eddyem/stm32samples/F1:F103/Hall_linear/readme

Take data from "Novotechnik TFD-4000" hall transducer and send it over CAN bus.
