eddyem/stm32samples/F0:F030,F042,F072/usbcan_ringbuffer/Readme.md

Simple code for CAN/USB development board
Simultaneous work of USB CDC (PL2303 emulation) and CAN

Pinout:
PB0 - LED0 - short blink when message received 
PB1 - LED1 - shine when line OK

PB8, PB9 - CAN Rx/Tx

PA11, PA12 - USB DM/DP
