eddyem/stm32samples/G0:G070,G0B1/RTC/README

Simplest work with RTC

Proto:

C - set/print calibration ticks (-511..+512) to each 2^20 ticks
Sd - set date (YY MM DD Weekday)
St - set time (HH MM SS)
t - print current Tms
T - print current Time

Button press - print current time @ usart3
