eddyem/stm32samples/F4:F401/blink/Readme

Simple blink with LED on PC13 (Olimex E407 development board)
