eddyem/stm32samples/F1:F103/canUART/Readme.md

CAN bus (PB8/PB9) <> UART1 (PA9/PA10)
The same thing as canusb for STM32F0x2

Baudrate - 921600
