eddyem/stm32samples/F3:F303/usart1fullDMA/Readme

Full Rx and Tx DMA, Rx DMA ends on buffer end or when '\n' received by character match interrupt.
