eddyem/stm32samples/F1:F103/RGB_LED_Screen/Readme

HUB75E-based RGB LED panel management

886 color (RRRGGGBB)

// the better fonts management is in Chronometer-v3
