eddyem/stm32samples/F1:F103/DS18/Readme

Timer1 + DMA to work with DS18/DHT11 sensors
#define DHT11 in dht.h to change data format to DHT11
