eddyem/stm32samples/F1:F103/BMP180/Readme

Work with I2C temperature/pressure sensor BMP180
