eddyem/stm32samples/F1:F103/BMP280/Readme

Work with I2C temperature/pressure sensor BMP280 and temp/pres/humidity sensor BME280
