eddyem/stm32samples/F1:F103/DHT22_DHT11/Readme

Timer1 + DMA to work with DHT22/DHT11 sensors
#define DHT11 in dht.h to change data format to DHT11
