eddyem/stm32samples/F1:F103/SI7005_HTU21D/Readme

Work with I2C humidity/temperature sensors SI7005 & HTU21D
