eddyem/stm32samples/F1:F103/pl2303_snippet/Readme

Base USB-CDC snippet with PL2303 emulation
With functions of integer read & decimal print.
