eddyem/stm32samples/F1:F103/pwmtest/Readme

Generate signals on PA8 by PWM @ TIM1_CC1.
