eddyem/stm32samples/F0:F030,F042,F072/Snippets/Readme.md

Some snippets
=============

* Flash_EEPROM - EEPROM emulation in flash
* Jump2Boot.c - software init of bootloader
* printuhex.c - print uint32_t in HEX
* readint.c - read integer number in any (bin/hex/dec) system
