eddyem/stm32samples/F1:F103/LED_Screen/Readme

Management with matrixes of LED screens 32x16 (or another size) pixels (P10).
