eddyem/stm32samples/F0:F030,F042,F072/pl2303/Readme.md

Simple CDC for USB development board, emulates PL2303
