eddyem/stm32samples/F1:F103/uart/README

Toggle LED PB9 on STM32F103 development board once per second
Allow to turn on/off LED PB8 depending on user commands over USART (0/1) and check its state (s)
Show information in USART console about S2/S3 buttons pressed
USART: 115200 8n1
