eddyem/stm32samples/F0:F030,F042,F072/tsys01_nucleo/Readme

Example for STM32F042 nucleo working with TSYS-01 temperature sensor.
Every 5 second check temperature on two sensors with different addresses and show values by USART.
USART speed 115200.
