eddyem/stm32samples/F0:F030,F042,F072/htu21d_nucleo/Readme

Example for STM32F042 nucleo working with HTU-21D humidity/temperature sensor.
Every 1 second check humidity/temperature and show values by USART.
USART speed 115200.
