eddyem/stm32samples/F0:F030,F042,F072/blink/README

Toggle Green LED on STM32F042-nucleo depending on jumper @ D2 (PA12):
- no jumper == 'SOS' in Morze
- with jumper - blink with period of 4 seconds
