eddyem/stm32samples/F0/uart/Readme

This is a simple USART over DMA application with hardware end of string control.
Speed 115200. Received string echoes back in reverce order.
