eddyem/stm32samples/F1/GPIO_TIM/README

simple FSMC emulation by timer interrupts
