eddyem/stm32samples/F1/2.8TFT/README

Template of USB-CDC

written for chinese devboard based on STM32F103R8T6

Press H for help
