eddyem/stm32samples/F1/keyboard_snippet/Readme.md

### USB HID keyboard snippet

This snippet allows to emulate USB keyboard to send different messages as they where typed on simple keyboard
(usefull for multiplatform usage without any drivers setup)
