eddyem/stm32samples/F1/GPS+ultrasonic/README

GPS-based timelapse tool
Connect up to four sensors (ultrasonic, infrared, laser and simple switch)
and get precision (milliseconds) time of their signals

written for chinese devboard based on STM32F103RBT6

Press H for help
