eddyem/stm32samples/F1/GPS/README

NOT READY!

GPS RTC

written for chinese devboard based on STM32F103RBT6

Press H for help
