eddyem/stm32samples/F1/simple_cdc/README

Very simple USB-CDC

written for chinese devboard based on STM32F103RBT6

Press H for help
