eddyem/stm32samples/F0:F030,F042,F072/CANbus_stepper/kicad/Readme.md

# CAN bus stepper controller

Move one stepper (12..36V) by CAN or USB bus.
