eddyem/stm32samples/F0:F030,F042,F072/3steppersLB/stepper_driver/04.jpg

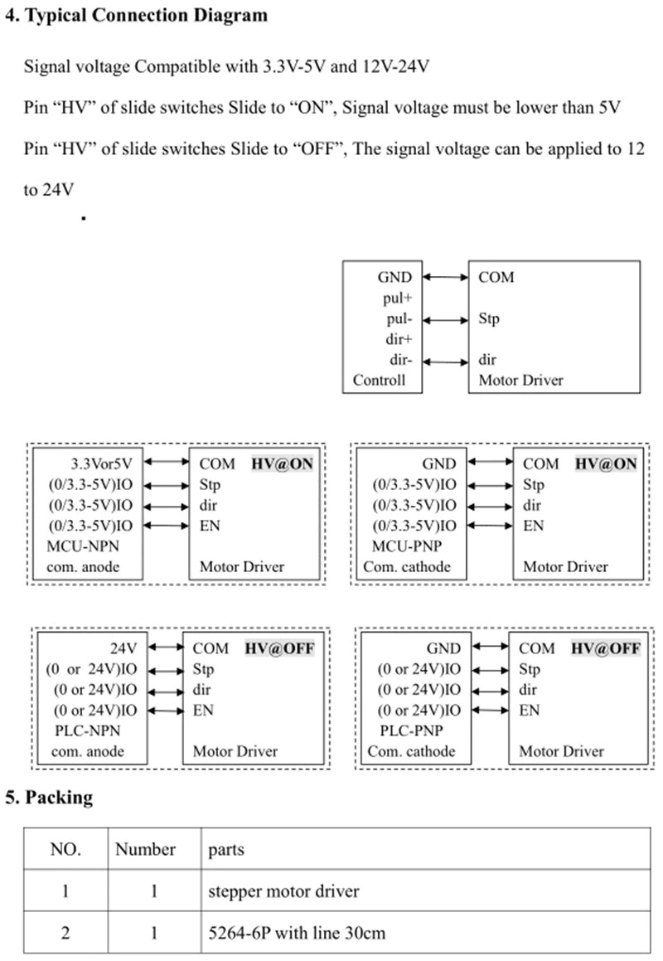
F0:F030,F042,F072/3steppersLB/stepper_driver/04.jpg
