eddyem/stm32samples/F0:F030,F042,F072/Chiller/kicad/Chiller_controlb.png

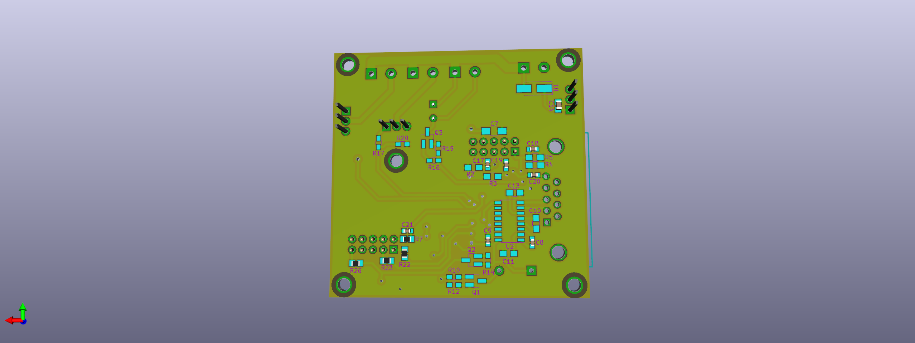
F0:F030,F042,F072/Chiller/kicad/Chiller_controlb.png
