eddyem/stm32samples/F0:F030,F042,F072/Socket_fans/knots/piecevise_files/6NNZZQ4uBDQ.jpg

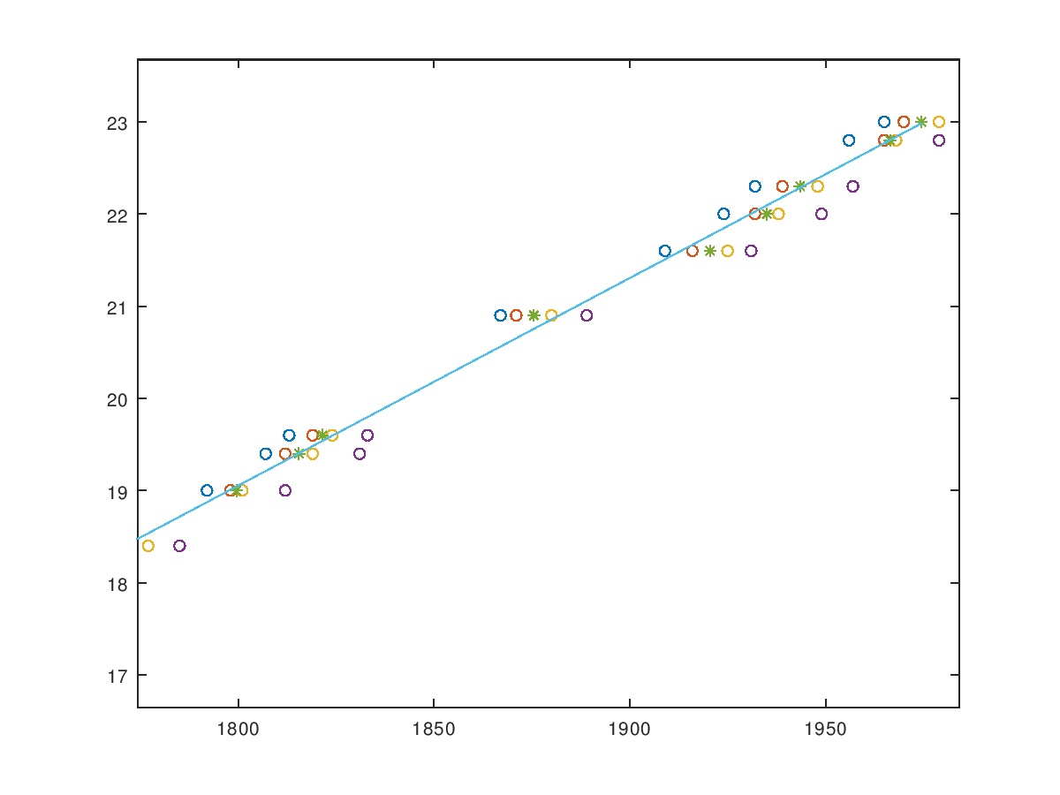
F0:F030,F042,F072/Socket_fans/knots/piecevise_files/6NNZZQ4uBDQ.jpg
