eddyem/stm32samples/F0:F030,F042,F072/Socket_fans/knots/piecevise_files/aLpoeyGgLuE.jpg

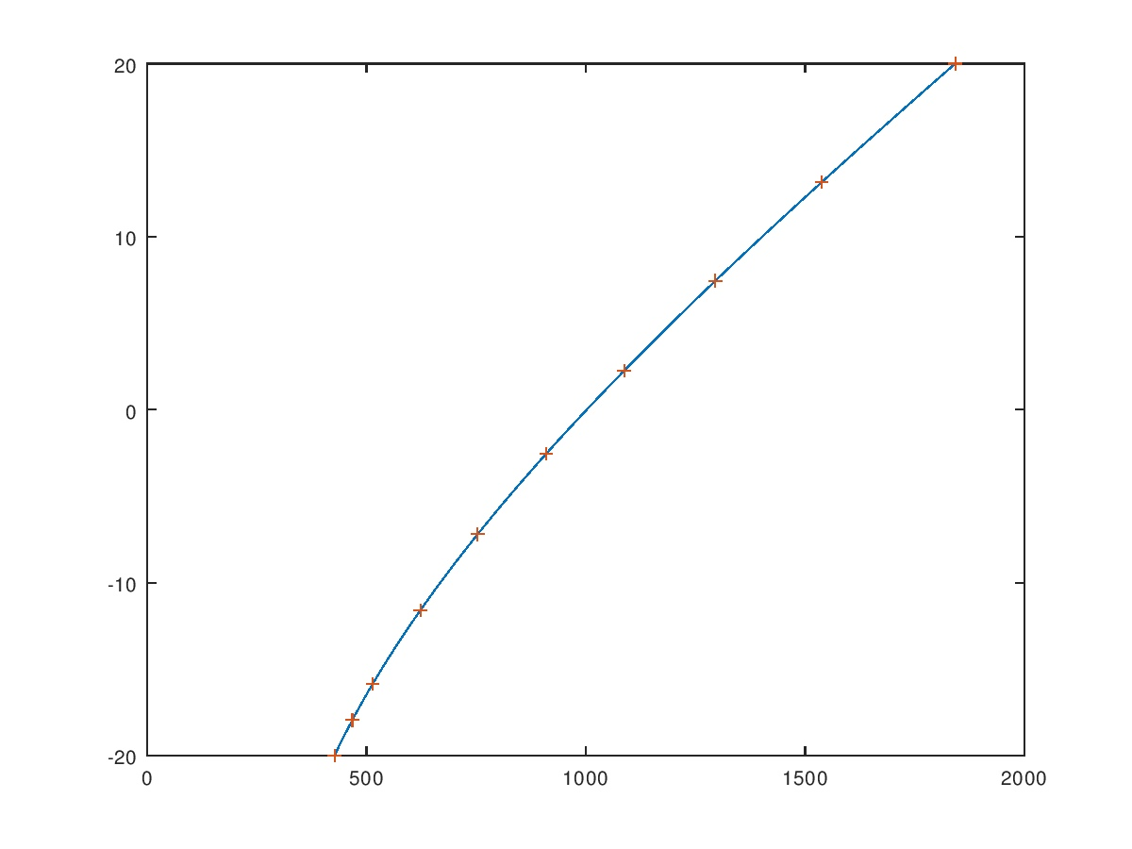
F0:F030,F042,F072/Socket_fans/knots/piecevise_files/aLpoeyGgLuE.jpg
