eddyem/stm32samples/F0:F030,F042,F072/Socket_fans/knots/piecevise_files/Dt9WEEJl_K8.jpg

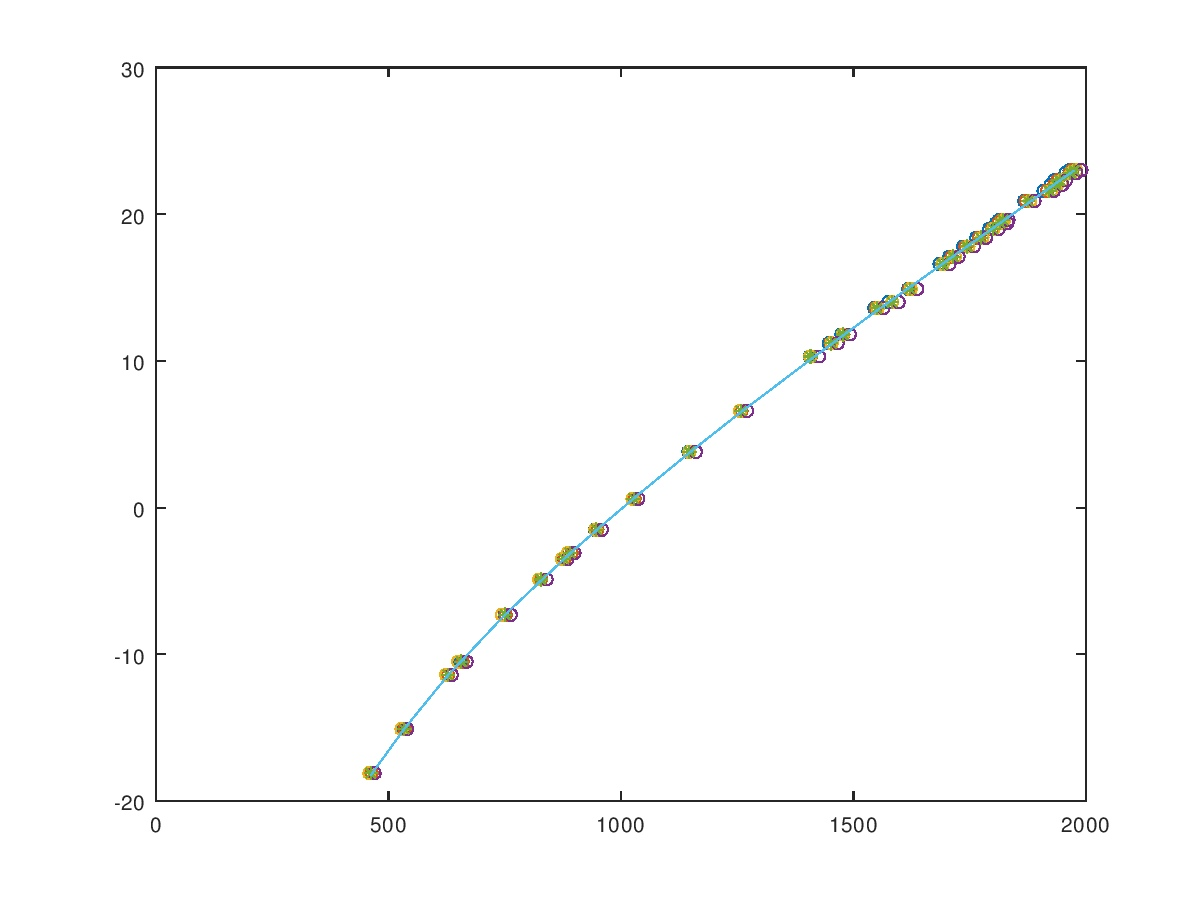
F0:F030,F042,F072/Socket_fans/knots/piecevise_files/Dt9WEEJl_K8.jpg
