eddyem/stm32samples/F0:F030,F042,F072/usbcan/kicad_new/Back.jpg

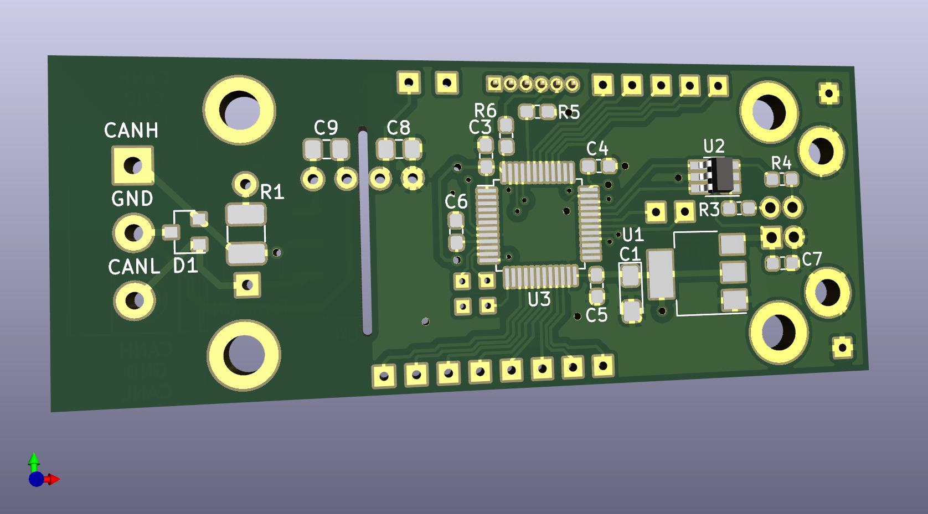
F0:F030,F042,F072/usbcan/kicad_new/Back.jpg
