eddyem/stm32samples/F0:F030,F042,F072/usbcan/kicad_new/Front.jpg

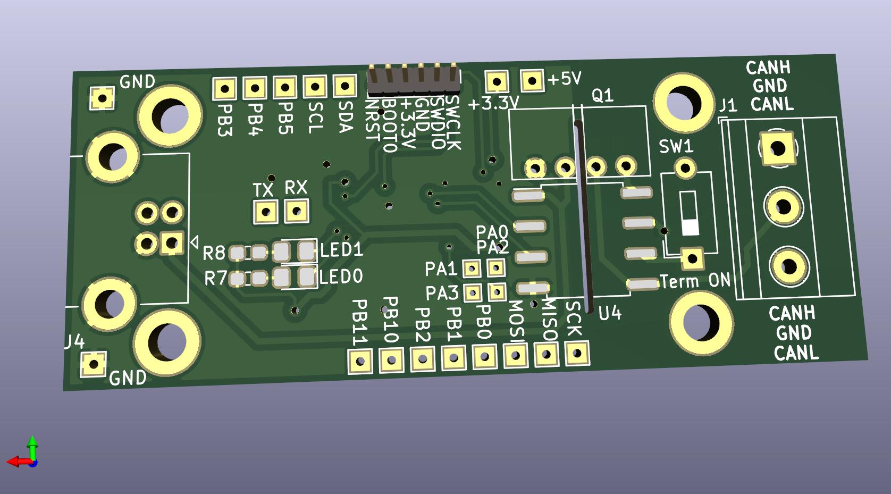
F0:F030,F042,F072/usbcan/kicad_new/Front.jpg
