eddyem/stm32samples/F0:F030,F042,F072/usbcan_relay/kicad/Board3D-back.jpg

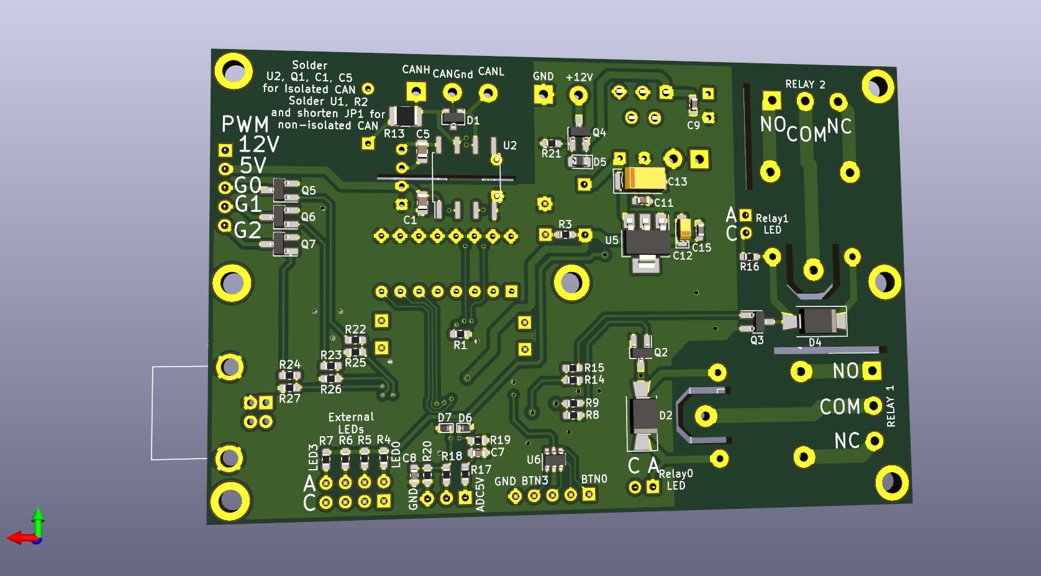
F0:F030,F042,F072/usbcan_relay/kicad/Board3D-back.jpg
