eddyem/stm32samples/F1:F103/CAR_CANbus/WindShield/kicad/Front.jpg

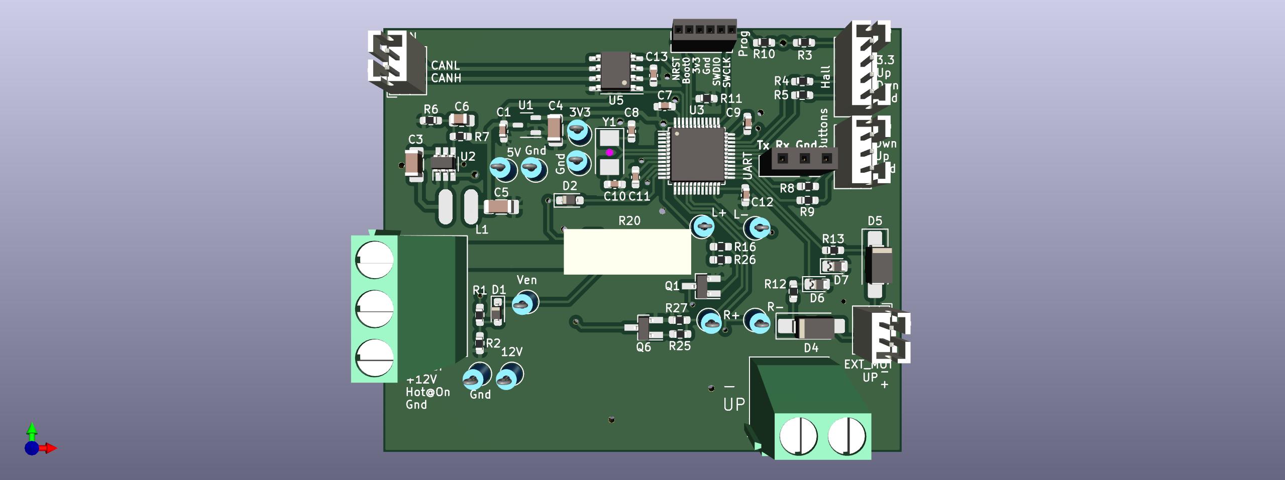
F1:F103/CAR_CANbus/WindShield/kicad/Front.jpg
