eddyem/stm32samples/F1:F103/RGB_LED_Screen/histo.png

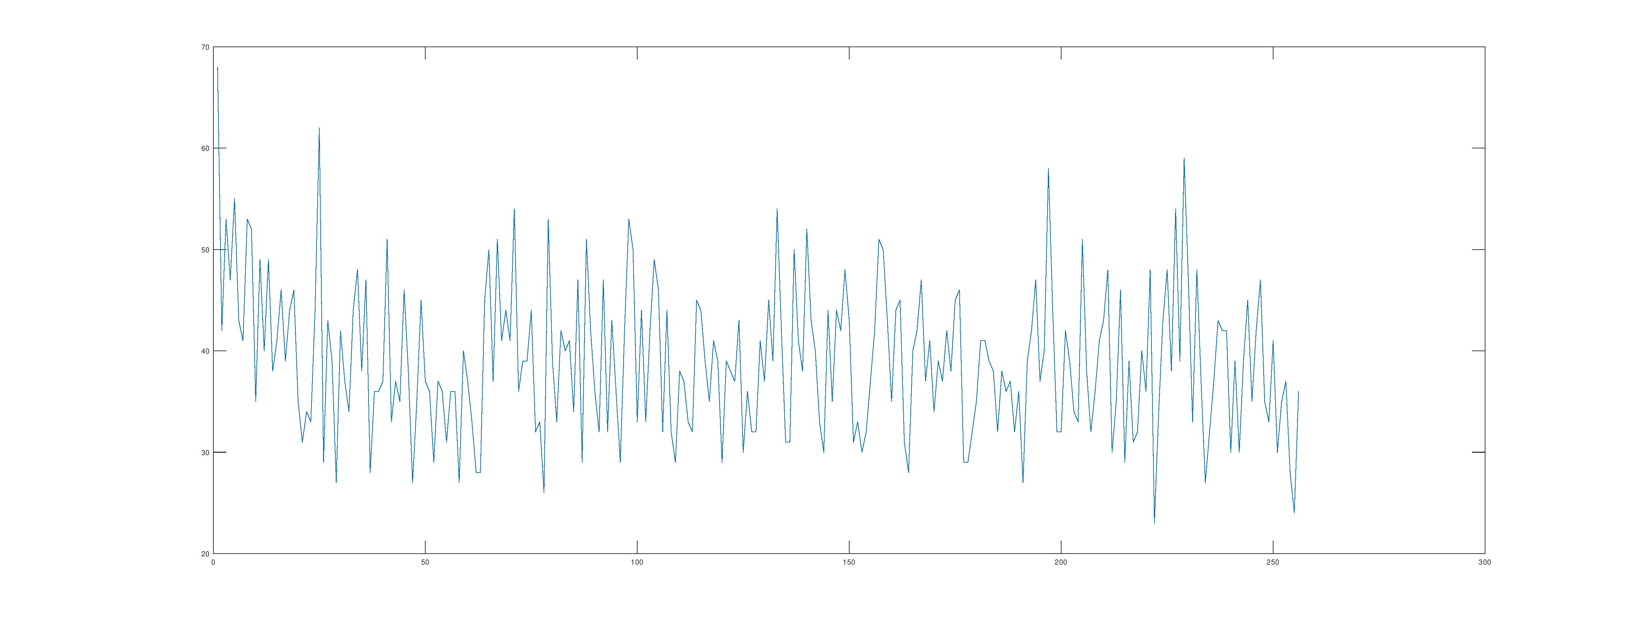
F1:F103/RGB_LED_Screen/histo.png
