eddyem/stm32samples/F1:F103/RGB_LED_Screen/img/p4.gif

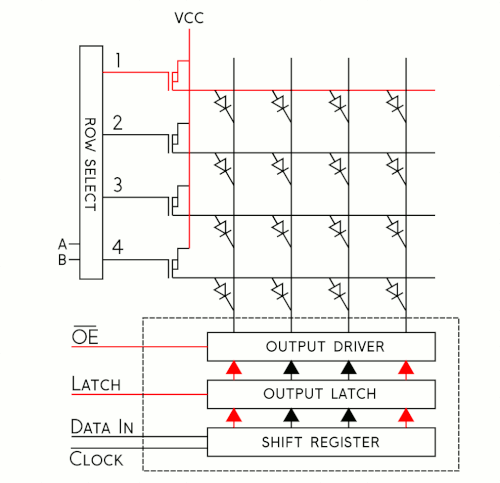
F1:F103/RGB_LED_Screen/img/p4.gif
