eddyem/stm32samples/F1:F103/shutter/kicad/3d.png

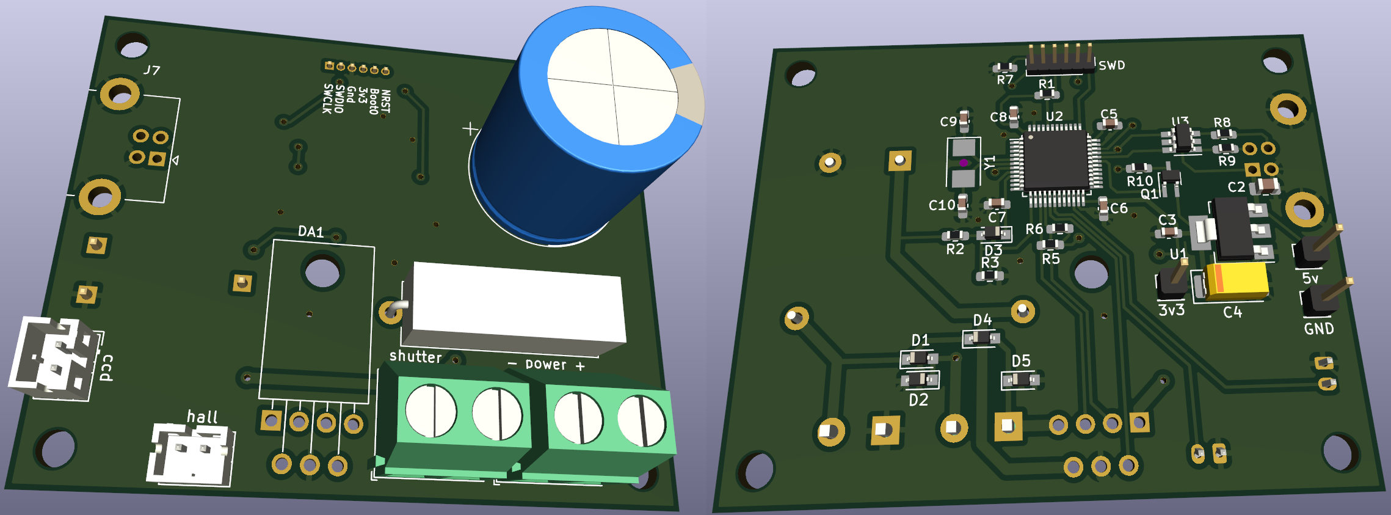
F1:F103/shutter/kicad/3d.png
