eddyem/stm32samples/F1:F103/shutter/UNISTABLE/kicad/qr.jpg

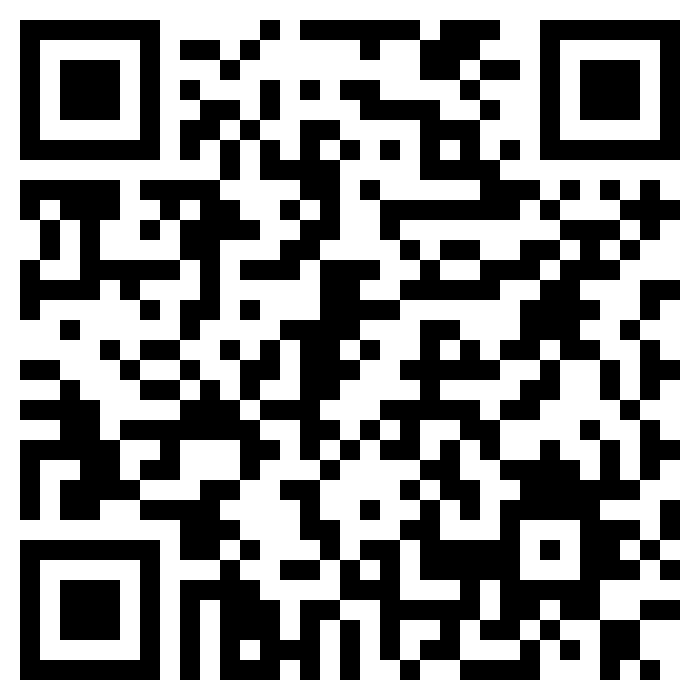
F1:F103/shutter/UNISTABLE/kicad/qr.jpg
