eddyem/stm32samples/F3:F303/CANbus4BTA/kicad/BAck.png

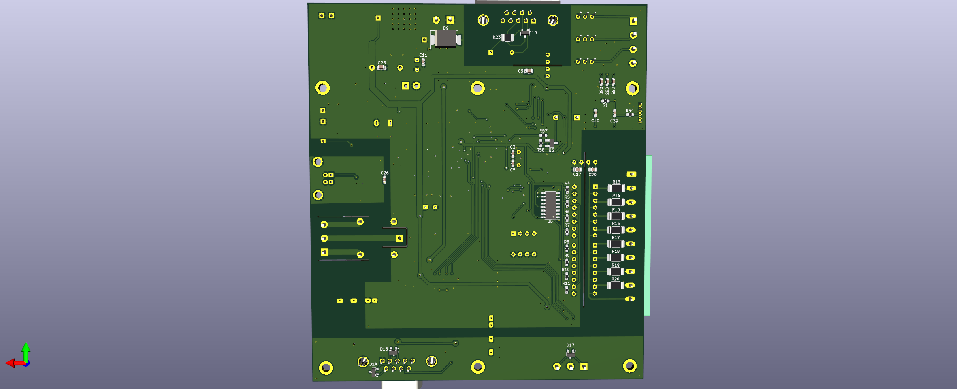
F3:F303/CANbus4BTA/kicad/BAck.png
