eddyem/stm32samples/F3:F303/CANbus4BTA/kicad/Front.png

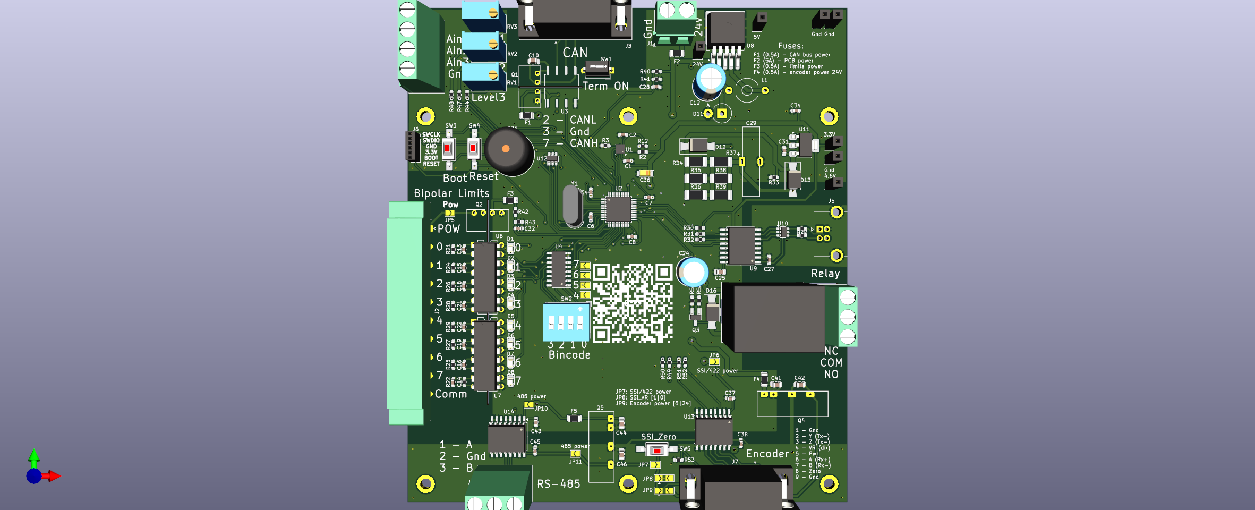
F3:F303/CANbus4BTA/kicad/Front.png
