eddyem/stm32samples/F3:F303/CANbus4BTA/kicad/QR.png

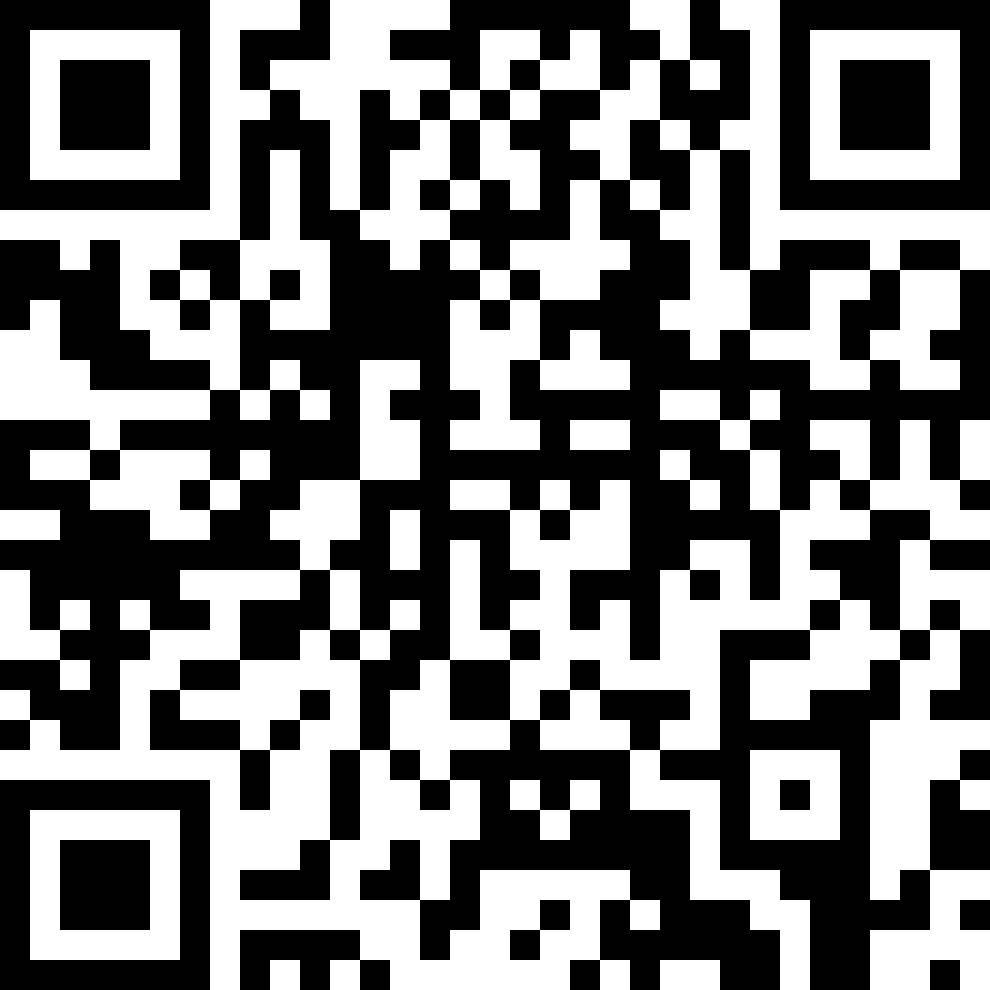
F3:F303/CANbus4BTA/kicad/QR.png
