eddyem/stm32samples/F3:F303/Multistepper/kicad/back.jpg

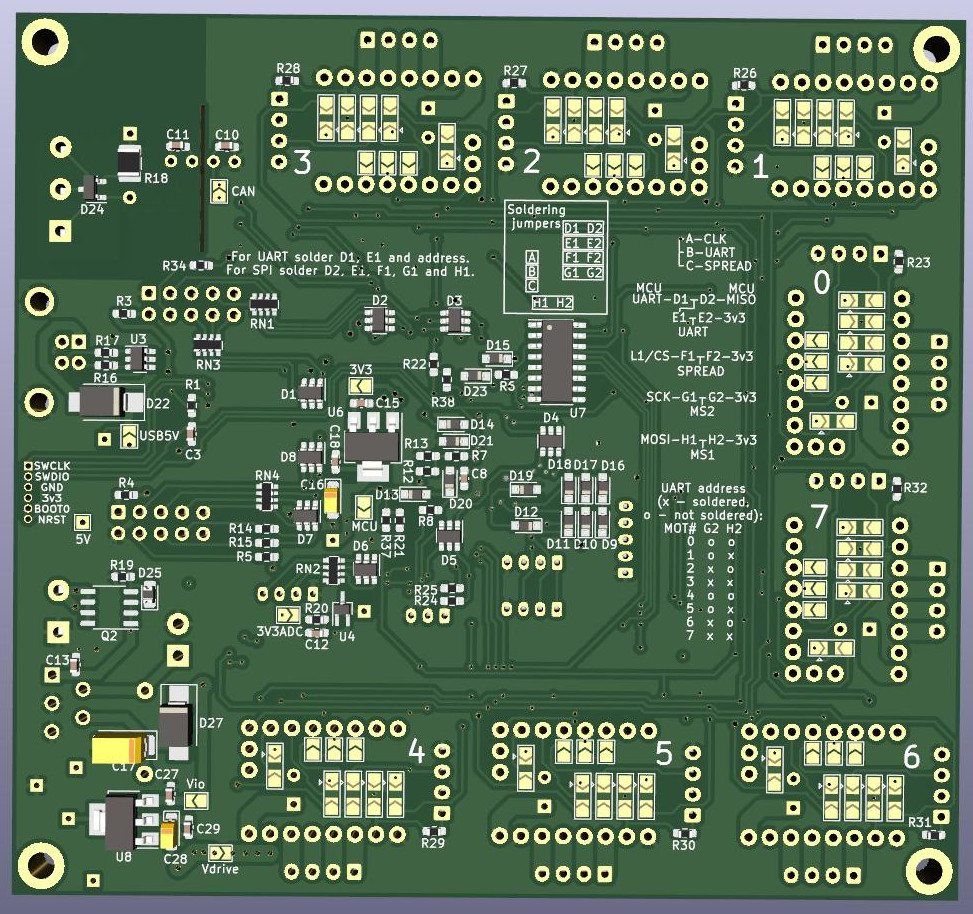
F3:F303/Multistepper/kicad/back.jpg
