eddyem/stm32samples/F3:F303/Multistepper/kicad/front.jpg

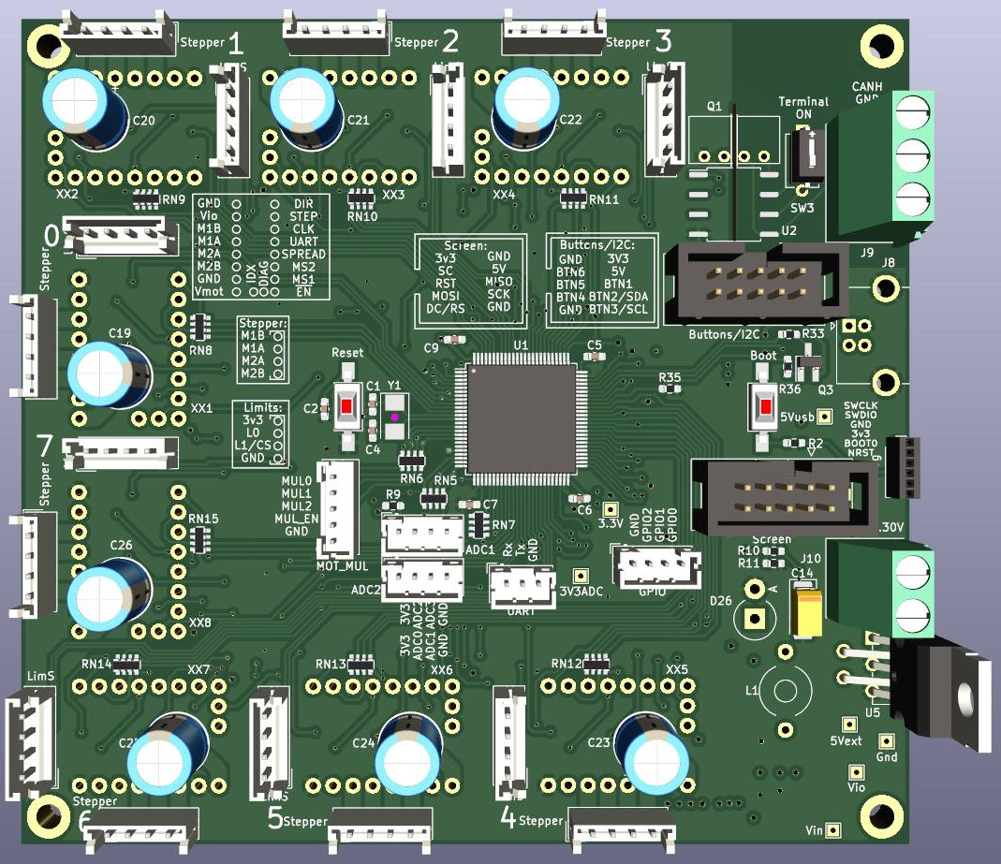
F3:F303/Multistepper/kicad/front.jpg
