eddyem/stm32samples/F3:F303/NitrogenFlooding/kicad/nitrogen/BOM.ods

Item | Qty | Reference(s) | Value | Footprint
1 | 4 | C1, C4, C9, C12 | 1u | 0603
2 | 2 | C2, C3 | 6 | 0603
3 | 12 | C5, C6, C7, C8, C10, C11, C13, C14, C16, C19, C20, C22 | 0.1 | 0603
4 | 1 | C15 | 47u 35V | 6032
5 | 2 | C17, C21 | 47u 6V | 3216
6 | 1 | C18 | 47u 10V | 6032
7 | 4 | D1, D2, D3, D4 | SS14 | SMA
8 | 1 | D5 | MBRS130L | SMB
9 | 2 | D6, D7 | PESD1CAN | SOT-23
10 | 1 | D8 | CESD3v3 | SOD-523
11 | 3 | D9, D10, D13 | SP0505BAHT | SOT-23-6
12 | 1 | D11 | MM3Z7V5 | 0805
13 | 1 | D12 | 1N5822 | DO-201
14 | 5 | J1, J5, J12, J14, J15 |  | JST_EH_B3B-EH-A_1x03_P2.50mm_Vertical
15 | 3 | J2, J3, J13 |  | MKDS-1,5-2_1x02_P5.00mm_Horizontal
16 | 3 | J4, J10, J11 | IDC2.54_02x05 | IDC-Header_2x05_P2.54mm_Vertical
17 | 1 | J6 | ADCext | JST_EH_B4B-EH-A_1x04_P2.50mm_Vertical
18 | 1 | J8 | USB_B | USB B
19 | 2 | J9, J18 |  | JST_EH_B5B-EH-A_1x05_P2.50mm_Vertical
20 | 1 | J16 | buzzer | Connector_PinSocket_2.54mm:PinSocket_1x02_P2.54mm_Vertical
21 | 1 | L1 | 100u | Toroid 1.5F
22 | 1 | L2 | 2.5k@100MHz | L_0805_2012Metric_Pad1.15x1.40mm_HandSolder
23 | 4 | Q1, Q2, Q3, Q4 | AOD4184 | TO-252-2
24 | 1 | Q5 | DTA114Y | SOT-323
25 | 1 | Q6 | SI2300 | SOT-23
26 | 1 | Q8 | IRF9310 | SO-8
27 | 1 | Q9 | SI2305 | SOT-23
28 | 6 | R1, R10, R21, R22, R24, R54 | 330 | 0603
29 | 4 | R2, R4, R6, R8 | 510 | 0603
30 | 8 | R3, R5, R7, R9, R11, R12, R39, R41 | 10k | 0603
31 | 1 | R13 | 1k5 | 0603
32 | 12 | R14, R16, R17, R20, R26, R27, R40, R42, R43, R45, R46, R47 | 6.8 | 0603
33 | 2 | R15, R18 | 22 | 0603
34 | 1 | R19 | 120 | 1210
35 | 4 | R23, R25, R38, R44 | 4k7 | 0603
36 | 10 | R28, R29, R30, R31, R32, R33, R34, R35, R36, R37 | 1k 0.1% | 0805
37 | 5 | RN1, RN2, RN3, RN4, RN5 | 330 | R_Array_Convex_4x0603
38 | 1 | U1 | MCP2551-I-SN | SOIC-8
39 | 1 | U2 | USBLC6-2SC6 | SOT-23-6
40 | 1 | U3 | MAX3485 | SO-8
41 | 1 | U4 | STM32F302VBTx | LQFP-100
42 | 1 | U5 | BME280 | LGA-8_2.5x2.5mm_P0.65mm_ClockwisePinNumbering
43 | 1 | U6 | LM2576HVS-5 | TO-263-5
44 | 2 | U7, U8 | LM1117-3.3 | SOT-223-3
45 | 1 | Y1 | NX5032GA-8MHz | Crystal_SMD_5032-2Pin_5.0x3.2mm
