eddyem/stm32samples/F1:F103/shutter/kicad/shutter.ods

Item | Qty | Reference(s) | Value | Footprint
1 | 1 | C1 | 2200u, 40V | Capacitor_THT:CP_Radial_D17.0mm_P7.50mm
2 | 1 | C2 | 1u | Capacitor_SMD:C_0805_2012Metric_Pad1.18x1.45mm_HandSolder
3 | 5 | C3, C5, C6, C7, C8 | 0.1 | Capacitor_SMD:C_0603_1608Metric_Pad1.08x0.95mm_HandSolder
4 | 1 | C4 | 47u | Capacitor_Tantalum_SMD:CP_EIA-6032-28_Kemet-C_Pad2.25x2.35mm_HandSolder
5 | 2 | C9, C10 | 6 | Capacitor_SMD:C_0603_1608Metric_Pad1.08x0.95mm_HandSolder
6 | 5 | D1, D2, D3, D4, D5 | 1N5819 | Diode_SMD:D_SOD-323_HandSoldering
7 | 1 | DA1 | TLE5205 | Package_TO_SOT_THT:TO-220-7_P2.54x3.8mm_StaggerEven_Lead5.85mm_TabDown
8 | 4 | H1, H2, H3, H4 | MountingHole | MountingHole:MountingHole_3.2mm_M3
9 | 1 | J1 | shutter | TerminalBlock_Phoenix:TerminalBlock_Phoenix_MKDS-1,5-2-5.08_1x02_P5.08mm_Horizontal
10 | 1 | J2 | power | TerminalBlock_Phoenix:TerminalBlock_Phoenix_MKDS-1,5-2-5.08_1x02_P5.08mm_Horizontal
11 | 1 | J3 | SWD | Connector_PinHeader_1.27mm:PinHeader_1x06_P1.27mm_Vertical
12 | 1 | J4 | 5v | Connector_PinHeader_2.54mm:PinHeader_1x01_P2.54mm_Vertical
13 | 1 | J5 | GND | Connector_PinHeader_2.54mm:PinHeader_1x01_P2.54mm_Vertical
14 | 1 | J6 | 3v3 | Connector_PinHeader_2.54mm:PinHeader_1x01_P2.54mm_Vertical
15 | 1 | J7 | USB_B | Connector_USB:USB_B_Lumberg_2411_02_Horizontal
16 | 1 | J8 | hall | Connector_JST:JST_PH_B2B-PH-K_1x02_P2.00mm_Vertical
17 | 1 | J9 | ccd | Connector_JST:JST_PH_B2B-PH-K_1x02_P2.00mm_Vertical
18 | 1 | Q1 | DTA114Y | Package_TO_SOT_SMD:SOT-323_SC-70_Handsoldering
19 | 1 | R1 | 6.9 | Resistor_SMD:R_0603_1608Metric_Pad0.98x0.95mm_HandSolder
20 | 1 | R2 | 56k | Resistor_SMD:R_0603_1608Metric_Pad0.98x0.95mm_HandSolder
21 | 3 | R3, R5, R6 | 4k7 | Resistor_SMD:R_0603_1608Metric_Pad0.98x0.95mm_HandSolder
22 | 1 | R4 | 300 II | Resistor_THT:R_Axial_Power_L20.0mm_W6.4mm_P22.40mm
23 | 1 | R7 | 10k | Resistor_SMD:R_0603_1608Metric_Pad0.98x0.95mm_HandSolder
24 | 2 | R8, R9 | 22 | Resistor_SMD:R_0603_1608Metric_Pad0.98x0.95mm_HandSolder
25 | 1 | R10 | 1k5 | Resistor_SMD:R_0603_1608Metric_Pad0.98x0.95mm_HandSolder
26 | 1 | U1 | LM1117-3.3 | Package_TO_SOT_SMD:SOT-223-3_TabPin2
27 | 1 | U2 | STM32F103C6Tx | Package_QFP:LQFP-48_7x7mm_P0.5mm
28 | 1 | U3 | USBLC6-2SC6 | Package_TO_SOT_SMD:SOT-23-6_Handsoldering
29 | 1 | Y1 | NX5032GA-8MHz | Crystal:Crystal_SMD_5032-2Pin_5.0x3.2mm
