eddyem/stm32samples/F3:F303/NitrogenFlooding/kicad/nitrogen/BOM_need.ods

Item | Qty | Reference(s) | Value | Footprint | URL | price, rub
2 | 2 | C2, C3 | 6pF | 0603 | https://aliexpress.ru/item/1005002586405163.html | 60
3 | 12 | C5, C6, C7, C8, C10, C11, C13, C14, C16, C19, C20, C22 | 100nF | 0603 | https://aliexpress.ru/item/1005002586405163.html | 60
9 | 2 | D6, D7 | PESD1CAN | SOT-23 | https://aliexpress.ru/item/32729130746.html | 120
10 | 1 | D8 | CESD3v3 | SOD-523 | https://aliexpress.ru/item/1005005038800564.html | 190
34 | 1 | L2 | 1k@100MHz | 0805 | https://aliexpress.ru/item/1005003358483856.html | 140
35 | 4 | Q1, Q2, Q3, Q4 | AOD4184 | TO-252-2 | https://aliexpress.ru/item/32930995628.html (3 комплекта) | 255
37 | 1 | Q6 | SI2300 | SOT-23 | https://aliexpress.ru/item/1005002318674167.html | 80
38 | 1 | Q8 | IRF9310 | SO-8 | https://aliexpress.ru/item/4001271775767.html | 140
39 | 1 | Q9 | SI2305 | SOT-23 | https://aliexpress.ru/item/32301950979.html | 225
40 | 6 | R1, R10, R21, R22, R24, R54 | 330R | 0603 | https://aliexpress.ru/item/32381956570.html | 40
44 | 12 | R14, R16, R17, R20, R26, R27, R40, R42, R43, R45, R46, R47 | 6.8R | 0603 | https://aliexpress.ru/item/32381956570.html | 40
45 | 2 | R15, R18 | 22R | 0603 | https://aliexpress.ru/item/32381956570.html | 40
48 | 10 | R28, R29, R30, R31, R32, R33, R34, R35, R36, R37 | 1k 0.1% | 0805 | https://aliexpress.ru/item/1005002265807229.html | 370
49 | 5 | RN1, RN2, RN3, RN4, RN5 | 330R | 0603 array | https://aliexpress.ru/item/1005003529112557.html | 55
56 | 1 | U1 | MCP2551-I-SN | SOIC-8 | https://aliexpress.ru/item/32884055929.html | 270
57 | 1 | U2 | USBLC6-2SC6 | SOT-23-6 | https://aliexpress.ru/item/1005004329064099.html | 500
58 | 1 | U3 | MAX3485 | SO-8 | https://aliexpress.ru/item/32849514004.html | 180
60 | 1 | U5 | BME280 | LGA-8_2.5x2.5mm_P0.65mm | https://aliexpress.ru/item/1005004783213962.html | 2100
61 | 1 | U6 | LM2576HVS-5 | TO-263-5 | https://aliexpress.ru/item/1005004050844143.html | 310
 |  |  |  |  | sum: | 5175
