eddyem/stm32samples/F1:F103/F1_testbrd_deprecated/Readme.md

Simple test for STM32F103, blinking PA0/PA1, two user buttons (PA14 and PA15) and USB (PL2303 emulator) <> USART1 echo.
