eddyem/stm32samples/F3:F303/Multistepper/kicad_old/multistepper.pdf

Terminal on/off CAN
connectors

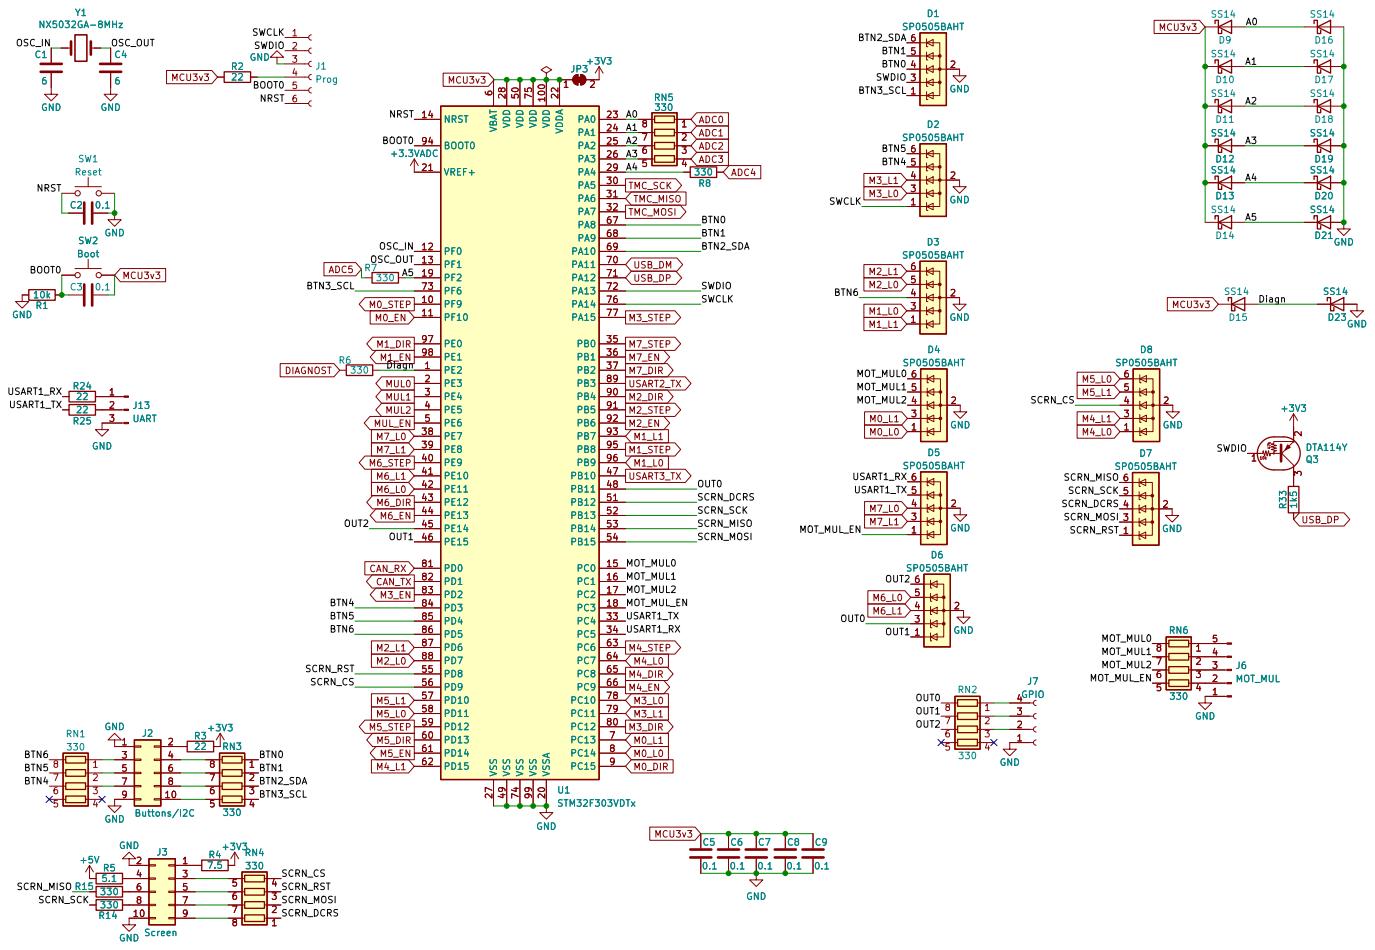
[picture p94: page 2]

7 7 | 2 2
6 6 | 3 3

1 5 5 | 6 6
2 7 7 | 7 7 8 8
3 9 | 6 6 10 10

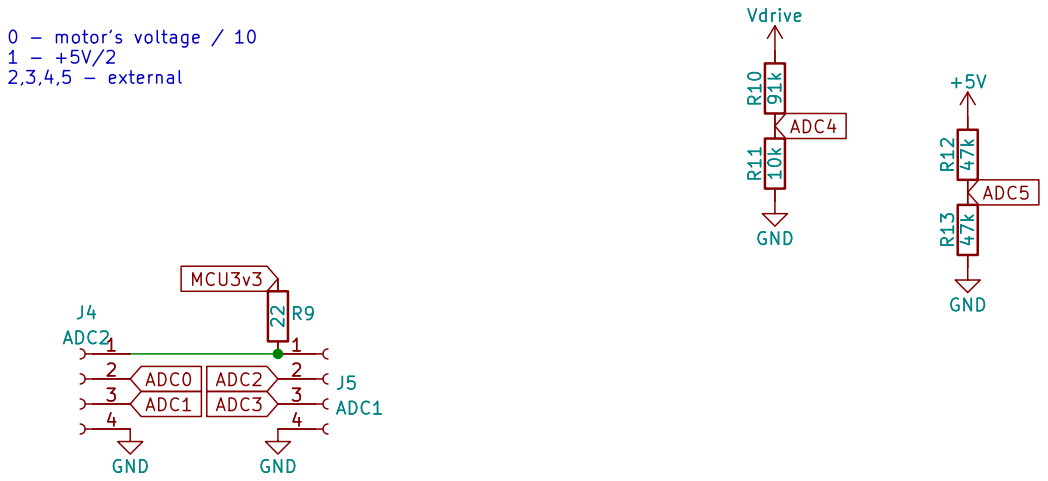
[picture p95: page 3]


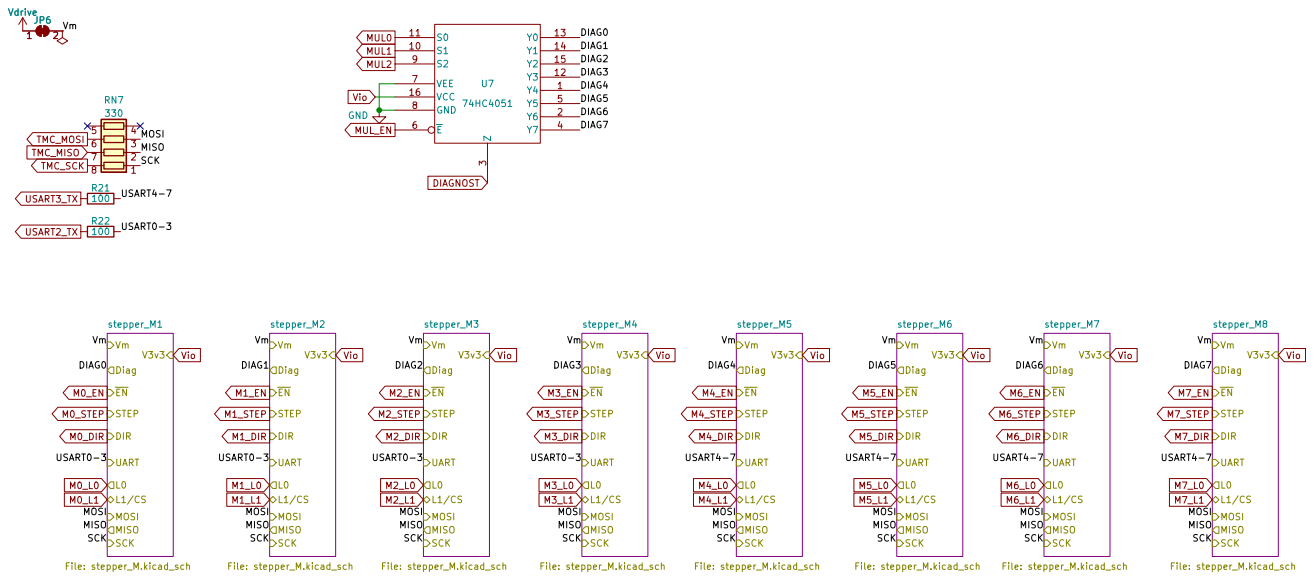
[picture p96: page 5]

stepper_M1
File: stepper_M.kicad_sch Vm
Diag
~{EN} STEP DIR MOSI MISO

stepper_M2

stepper_M3

stepper_M5

stepper_M6

stepper_M8

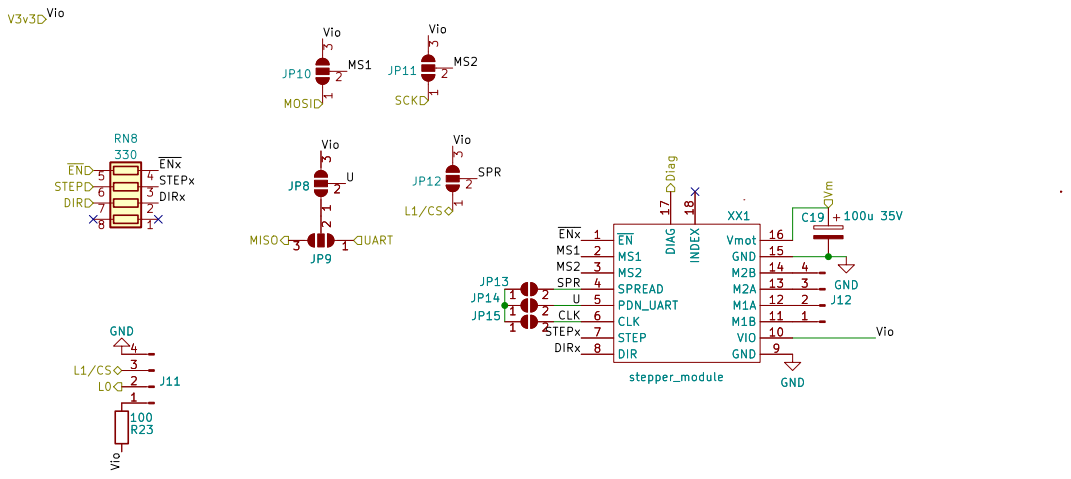
[picture p97: page 6]

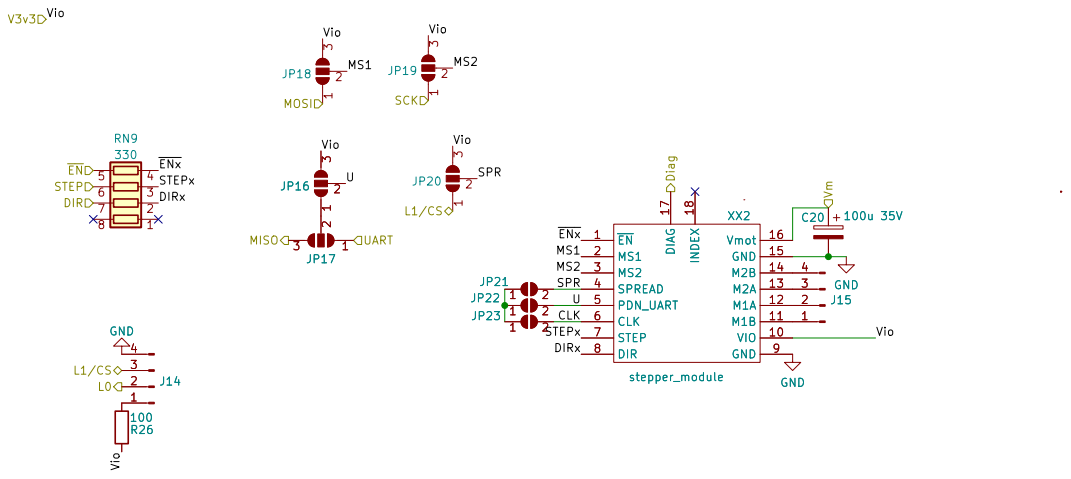
[picture p98: page 7]

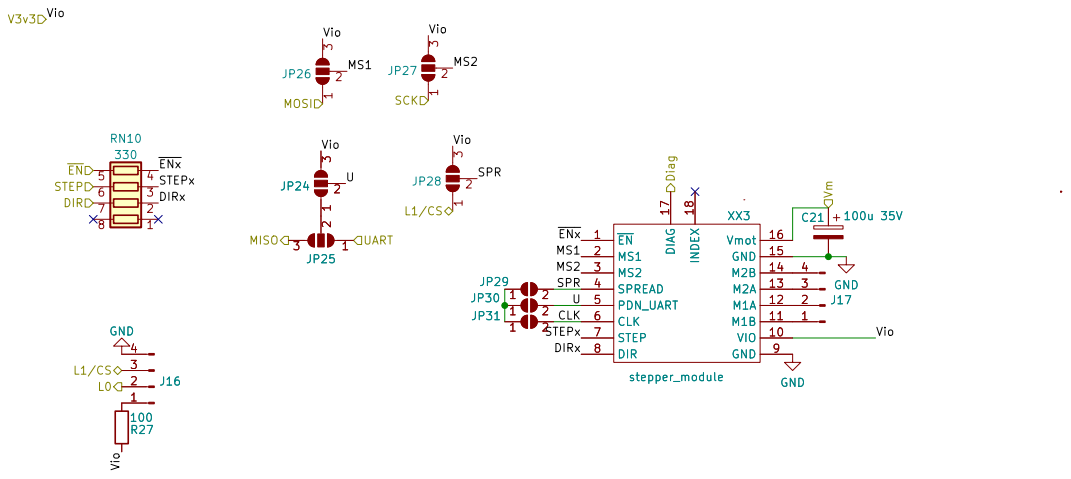
[picture p99: page 8]

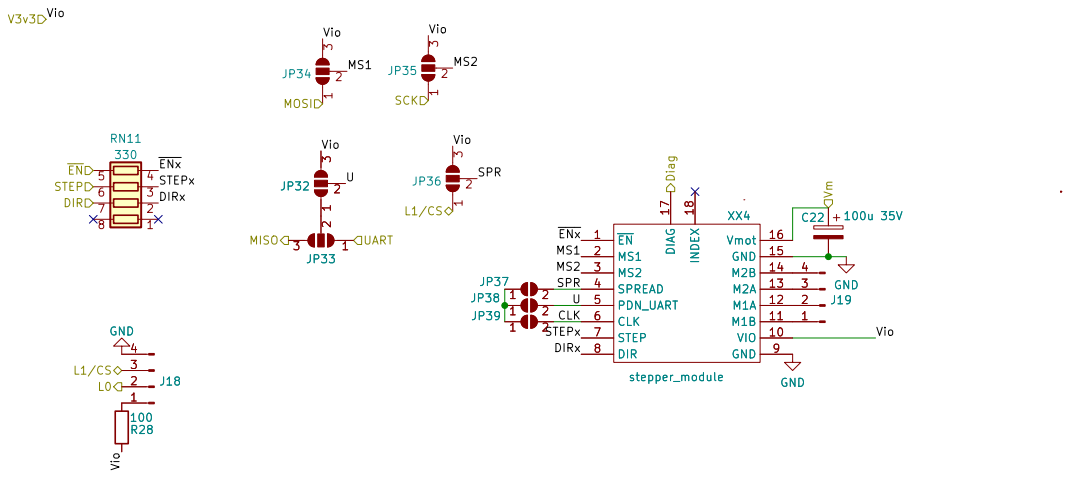
[picture p100: page 9]

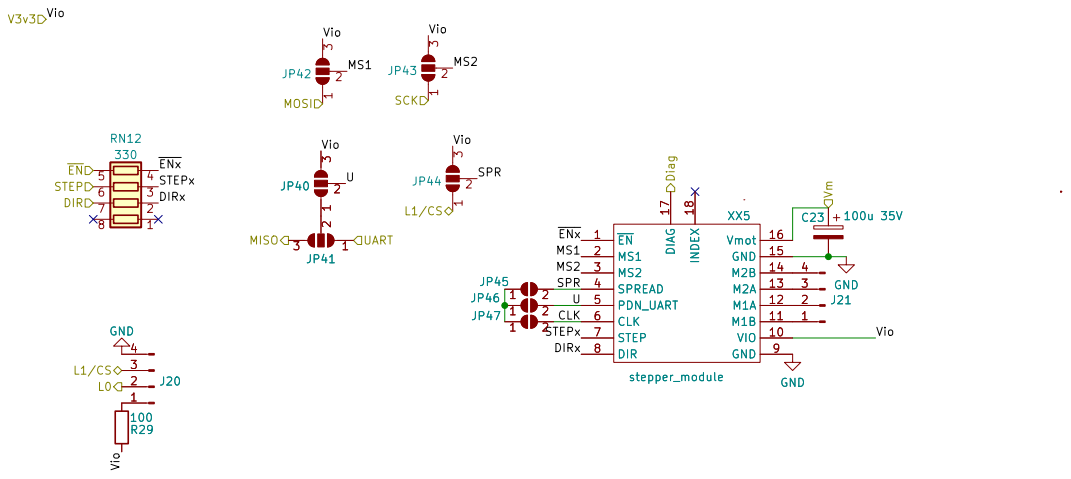
[picture p101: page 10]

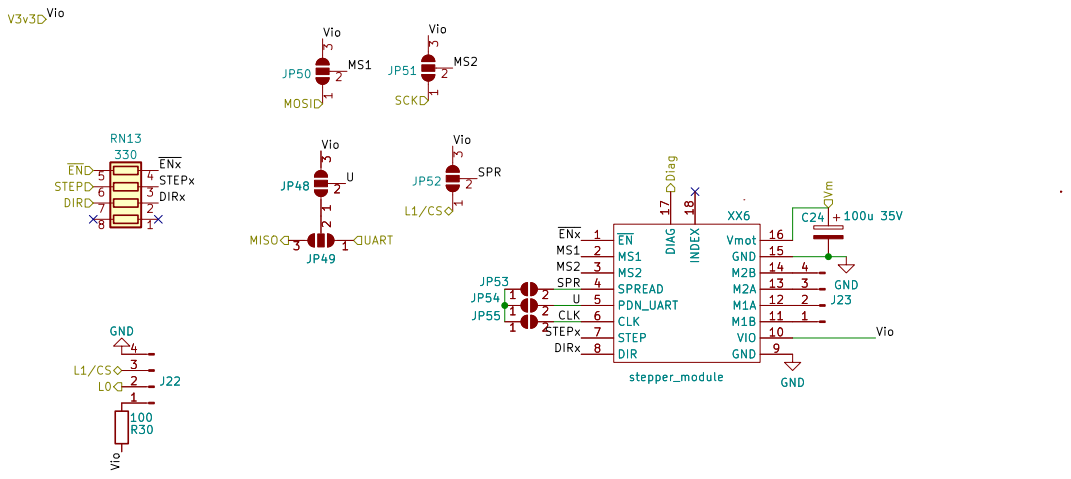
[picture p102: page 11]

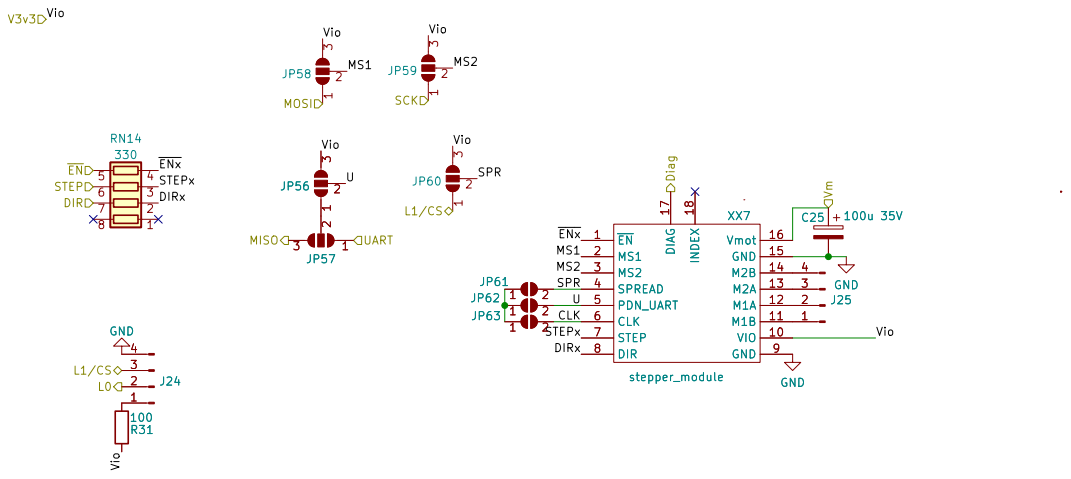
[picture p103: page 12]

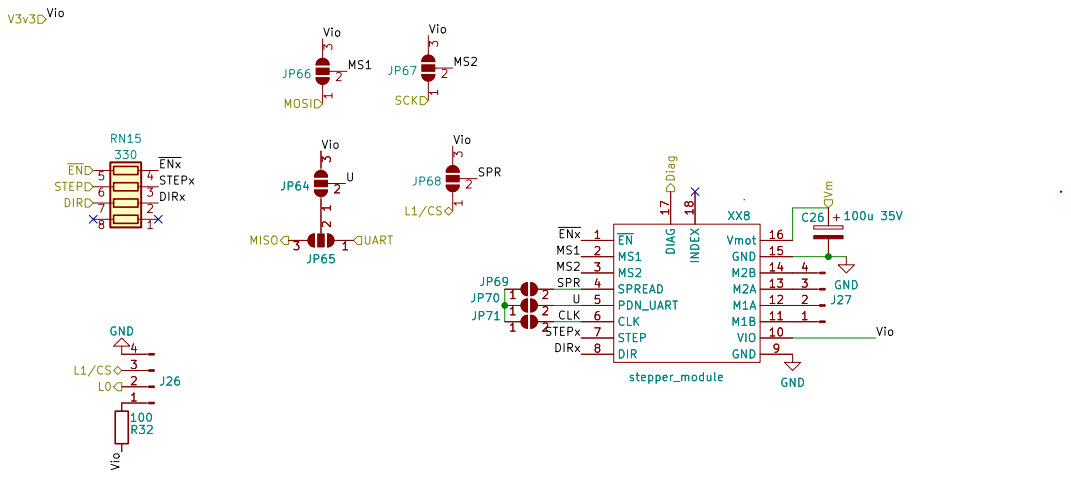
[picture p104: page 13]
