eddyem/stm32samples/F0:F030,F042,F072/usbcan_gpio/gpio.c

/*
 * This file is part of the usbcangpio project.
 * Copyright 2026 Edward V. Emelianov <edward.emelianoff@gmail.com>.
 *
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
 * You should have received a copy of the GNU General Public License
 * along with this program.  If not, see <http://www.gnu.org/licenses/>.
 */

#include <stm32f0.h>
#include <string.h>

#include "adc.h"
#include "flash.h"
#include "gpio.h"
#include "i2c.h"
#include "pwm.h"
#include "spi.h"
#include "usart.h"

static uint16_t monitor_mask[2] = {0}; // pins to monitor == 1 (ONLY GPIO and ADC)
static uint16_t oldstates[2][16] = {0}; // previous state (16 bits - as some pins could be analog)

// intermediate buffer to change pin's settings by user request; after checking in will be copied to the_conf
static pinconfig_t pinconfig[2][16] = {0};
static uint8_t pinconfig_notinited = 1; // ==0 after first memcpy from the_conf to pinconfig
#define CHKPINCONFIG()  do{if(pinconfig_notinited) chkpinconf();}while(0)

// TODO: remove AFmask, make function to get right AF number by pin's FuncValues
typedef struct{
    uint8_t funcs;  // bitmask according to enum FuncNames
    uint8_t AF[FUNC_AMOUNT]; // alternate function number for corresponding `FuncNames` number
} pinprops_t;

// AF for USART, SPI, I2C:
#define _U(x)  [FUNC_USART] = x
// _S(0) or _U(0) have no sence, but lets understand that this pin have SPI or USART
#define _S(x)  [FUNC_SPI] = x
#define _I(x)  [FUNC_I2C] = x
#define _P(x)  [FUNC_PWM] = x
// Here included only common AF for STM32F042 and STM32F072 and without negative timer outputs (stars - collisions)
static const pinprops_t pin_props[2][16] = {
    [0] = { // PORT A
        [0]  = { .funcs = 0b00000001, .AF = {0}}, // PA0: ADC0
        [1]  = { .funcs = 0b00010001, .AF = {_P(2)}}, // PA1: ADC1, AF2 (TIM2_CH2*)
        [2]  = { .funcs = 0b00010011, .AF = {_U(1), _P(2)}}, // PA2: ADC2, AF2 (TIM2_CH3**), AF1 (USART2_TX)
        [3]  = { .funcs = 0b00010011, .AF = {_U(1), _P(2)}}, // PA3: ADC3, AF2 (TIM2_CH4***), AF1 (USART2_RX)
        [5]  = { .funcs = 0b00000101, .AF = {_S(0)}}, // PA5: ADC5, AF9 (SPI1_SCK)
        [6]  = { .funcs = 0b00010101, .AF = {_S(0), _P(5)}}, // PA6: ADC6, AF0 (SPI1_MISO), AF5 (TIM16_CH1)
        [7]  = { .funcs = 0b00010101, .AF = {_S(0), _P(4)}}, // PA7: ADC7, AF0 (SPI1_MOSI), AF4 (TIM14_CH1)
        [9]  = { .funcs = 0b00010010, .AF = {_U(1), _P(2)}}, // PA9: AF1 (USART1_TX), AF2 (TIM1_CH2)
        [10] = { .funcs = 0b00010010, .AF = {_U(1), _P(2)}}, // PA10: AF1 (USART1_RX), AF2 (TIM1_CH3)
    },
    [1] = { // PORT B
        [0]  = { .funcs = 0b00010001, .AF = {_P(1)}}, // PB0: ADC8, AF1 (TIM3_CH3)
        [1]  = { .funcs = 0b00010001, .AF = {_P(1)}}, // PB1: ADC9, AF1 (TIM3_CH4)
        [2]  = { .funcs = 0b00000000, .AF = {0}}, // PB2: nothing except GPIO
        [3]  = { .funcs = 0b00010100, .AF = {_S(0), _P(2)}}, // PB3: AF0, (SPI1_SCK), AF2 (TIM2_CH2*)
        [4]  = { .funcs = 0b00010100, .AF = {_S(0), _P(1)}}, // PB4: AF0 (SPI1_MISO), AF1 (TIM3_CH1)
        [5]  = { .funcs = 0b00010100, .AF = {_S(0), _P(1)}}, // PB5: AF0 (SPI1_MOSI), AF1 (TIM3_CH2)
        [6]  = { .funcs = 0b00001010, .AF = {_U(0), _I(1)}}, // PB6: AF0 (USART1_TX), AF1 (I2C1_SCL)
        [7]  = { .funcs = 0b00001010, .AF = {_U(0), _I(1)}}, // PB7: AF0 (USART1_RX), AF1 (I2C1_SDA)
        [10] = { .funcs = 0b00011000, .AF = {_I(1), _P(2)}}, // PB10: AF1 (I2C1_SCL), AF2 (TIM2_CH3**)
        [11] = { .funcs = 0b00011000, .AF = {_I(1), _P(2)}}, // PB11: AF1 (I2C1_SDA), AF2 (TIM2_CH4***)
    }
};
#undef _U
#undef _S
#undef _I

#define CANADC(x)   ((x) & (1<<FUNC_AIN))
#define CANUSART(x) ((x) & (1<<FUNC_USART))
#define CANSPI(x)   ((x) & (1<<FUNC_SPI))
#define CANI2C(x)   ((x) & (1<<FUNC_I2C))
#define CANPWM(x)   ((x) & (1<<FUNC_PWM))

static uint8_t haveI2C = 0; // ==1 if chkpinconf found I2C
static uint8_t haveSPI = 0;

// return pin_props[port][pin].funcs for listing or -1 if disabled
int pinfuncs(uint8_t port, uint8_t pin){
    if(is_disabled(port, pin)) return -1;
    return (int) pin_props[port][pin].funcs;
}

/**
 * @brief get_usart_index - get USART index (0 or 1 for USART1 or USART2) by given pin
 * @param port
 * @param pin
 * @return -1 if error
 */
int get_usart_index(uint8_t port, uint8_t pin, usart_props_t *p){
    if(port > 1 || pin > 15 || !CANUSART(pin_props[port][pin].funcs)) return -1;
    int idx = -1;
    usart_props_t curprops = {0};
    if(port == 0){ // GPIOA
        switch(pin){
        case 2: // USART2_TX
            idx = 1;
            curprops.istx = 1;
            break;
        case 3: // USART2_RX
            idx = 1;
            curprops.isrx = 1;
            break;
        case 9: // USART1_TX
            idx = 0;
            curprops.istx = 1;
            break;
        case 10: // USART1_RX
            idx = 0;
            curprops.isrx = 1;
            break;
        default:
            break;
        }
    }else if(port == 1){ // GPIOB
        switch(pin){
        case 6: // USART1_TX
            idx = 0;
            curprops.istx = 1;
            break;
        case 7: // USART1_RX
            idx = 0;
            curprops.isrx = 1;
            break;
        default:
            break;
        }
    }
    if(p) *p = curprops;
    return idx;
}

// return -1 if pin can't I2C, or return 0 and fill `p`
int get_i2c_index(uint8_t port, uint8_t pin, i2c_props_t *p){
    if(port > 1 || pin > 15 || !CANI2C(pin_props[port][pin].funcs)) return -1;
    int idx = -1; // later we can add SPI2 support
    i2c_props_t curprops = {0};
    if(port == 1){ // only GPIOB
        switch(pin){
        case 6: // PB6 - I2C1_SCL
            idx = 0;
            curprops.isscl = 1;
            break;
        case 7: // PB7 - I2C1_SDA
            idx = 0;
            curprops.issda = 1;
            break;
        case 10: // PB10 - I2C1_SCL
            idx = 0;
            curprops.isscl = 1;
            break;
        case 11: // PB11 - I2C1_SDA
            idx = 0;
            curprops.issda = 1;
            break;
        default:
            break;
        }
    }
    if(p) *p = curprops;
    return idx;
}

int get_spi_index(uint8_t port, uint8_t pin, spi_props_t *p){
    if(port > 1 || pin > 15 || !CANSPI(pin_props[port][pin].funcs)) return -1;
    int idx = -1;
    spi_props_t curprops = {0};
    if(port == 0){ // PA5-7 (SCK-MISO-MOSI)
        switch(pin){
        case 5:
            idx = 0;
            curprops.issck =1;
            break;
        case 6:
            idx = 0;
            curprops.ismiso = 1;
            break;
        case 7:
            idx = 0;
            curprops.ismosi = 1;
            break;
        default: break;
        }
    }else if(port == 1){ // PB3-5 (SCK-MISO-MOSI)
        switch(pin){
        case 3:
            idx = 0;
            curprops.issck =1;
            break;
        case 4:
            idx = 0;
            curprops.ismiso = 1;
            break;
        case 5:
            idx = 0;
            curprops.ismosi = 1;
            break;
        default: break;
        }
    }
    if(p) *p = curprops;
    return idx;
}

// default config
static void defconfig(pinconfig_t *cfg){
    if(!cfg) return;
    cfg->af = FUNC_AIN;
    cfg->afno = 0;
    cfg->mode = MODE_INPUT;
    cfg->monitor = 0;
    cfg->speed = SPEED_LOW;
    cfg->pull = PULL_NONE;
}

// check current pin configuration; in case of errors set default values (floating input)
int chkpinconf(){
    int ret = TRUE;
    if(pinconfig_notinited){
        memcpy(pinconfig, the_conf.pinconfig, sizeof(pinconfig));
        pinconfig_notinited = 0;
    }
    usartconf_t UC;
    if(!get_curusartconf(&UC)){
        get_defusartconf(&UC);
    }else{ // got current config -> clear `RXen`, `TXen` and `monitor`: if none appeared, turn OFF USART!
        UC.RXen = 0; UC.TXen = 0; UC.monitor = 0;
    }
    int active_usart = -1; // number of USART if user selects it (we can't check it by UC->idx)
    int active_i2c = -1;
    int active_spi = -1;
    i2c_props_t i2cprops = {0};
    spi_props_t spiprops = {0};
    for(int port = 0; port < 2; ++port){
        for(int pin = 0; pin < 16; ++pin){
            pinconfig_t *cfg = &pinconfig[port][pin];
            if(!cfg->enable) continue;
            const pinprops_t *props = &pin_props[port][pin];
            // wrong configuration -> don't mind AF, make FLIN
            if(cfg->mode == MODE_AF){
                if(cfg->af >= FUNC_AMOUNT || !((1<<cfg->af) & props->funcs)){
                    DBG("Wrong AF config -> FL IN\n");
                    defconfig(cfg);
                    ret = FALSE;
                }else{ // set afno to proper number
                    cfg->afno = props->AF[cfg->af];
                    switch(cfg->af){
                    case FUNC_USART:{
                        usart_props_t up;
                        int usart_idx = get_usart_index(port, pin, &up);
                        if(usart_idx < 0){ // error -> defaults
                            DBG("no USART on this pin\n");
                            defconfig(cfg);
                            ret = FALSE;
                            break;
                        }
                        if(active_usart == -1){
                            active_usart = usart_idx;
                        }else if(active_usart != usart_idx){
                            // User tries to configure Rx/Tx on different USARTs
                            DBG("USART conflicted!\n");
                            defconfig(cfg);
                            ret = FALSE;
                            break;
                        }
                        if(up.isrx) UC.RXen = 1;
                        else if(up.istx) UC.TXen = 1;
                        if(cfg->monitor) UC.monitor = 1;
                    }
                        break;
                    case FUNC_PWM:{
                        pwmtimer_t pwm;
                        if(!canPWM(port, pin, &pwm)){
                            DBG("Can't PWM\n");
                            defconfig(cfg);
                            ret = FALSE;
                            break;
                        }
                        if(pwm.collision && pinconfig[pwm.collport][pwm.collpin].af == FUNC_PWM){
                            DBG("Found collision -> remove\n");
                            defconfig(&pinconfig[pwm.collport][pwm.collpin]); // set later collision to defaults
                            ret = FALSE;
                            break;
                        }
                    }
                        break;
                    case FUNC_I2C:{
                        i2c_props_t ip;
                        int i2c_idx = get_i2c_index(port, pin, &ip);
                        if(i2c_idx < 0){
                            defconfig(cfg);
                            ret = FALSE;
                            break;
                        }
                        // maybe for 2 I2Cs
                        if(active_i2c == -1) active_i2c = i2c_idx;
                        else if(active_i2c != i2c_idx){
                            // collision
                            defconfig(cfg);
                            ret = FALSE;
                            break;
                        }
                        if(ip.isscl){
                            if(i2cprops.isscl){ // two SCLs
                                defconfig(cfg);
                                ret = FALSE;
                                break;
                            }
                            i2cprops.isscl = 1;
                        }
                        if(ip.issda){
                            if(i2cprops.issda){ // two SDAs
                                defconfig(cfg);
                                ret = FALSE;
                                break;
                            }
                            i2cprops.issda = 1;
                        }
                    }
                        break;
                    case FUNC_SPI:{
                        spi_props_t sp;
                        int spi_idx = get_spi_index(port, pin, &sp);
                        if(spi_idx < 0){
                            defconfig(cfg);
                            ret = FALSE;
                            break;
                        }
                        if(active_spi == -1) active_spi = spi_idx;
                        else if(active_spi != spi_idx){
                            defconfig(cfg);
                            ret = FALSE;
                            break;
                        }
                        if(sp.issck){
                            if(spiprops.issck){
                                defconfig(cfg);
                                ret = FALSE;
                                break;
                            }
                            spiprops.issck = 1;
                        }
                        if(sp.ismiso){
                            if(spiprops.ismiso){
                                defconfig(cfg);
                                ret = FALSE;
                                break;
                            }
                            spiprops.ismiso = 1;
                        }
                        if(sp.ismosi){
                            if(spiprops.ismosi){
                                defconfig(cfg);
                                ret = FALSE;
                                break;
                            }
                            spiprops.ismosi = 1;
                        }
                    }
                        break;
                    default: break; // later fill other functions
                    }
                }
            }
        }
    }
    // now check USART configuration
    if(active_usart != -1){
        DBG("Got active USART\n");
        UC.idx = active_usart;
        if(!chkusartconf(&UC)) ret = FALSE;
    }else{
        DBG("No active USARTs\n");
        get_defusartconf(&UC); // clear global configuration
        the_conf.usartconfig = UC;
    }
    // check active I2C
    if(active_i2c != -1){
        if(i2cprops.isscl && i2cprops.issda){
            haveI2C = 1;
        }else{
            DBG("Need two pins for I2C\n");
            ret = FALSE;
            haveI2C = 0;
        }
    }
    if(active_spi != -1){
        if(spiprops.issck && (spiprops.ismiso || spiprops.ismosi)){
            haveSPI = 1;
            if(!spiprops.ismosi) the_conf.spiconfig.rxonly = 1;
            else the_conf.spiconfig.rxonly = 0;
            if(!spiprops.ismiso) the_conf.spiconfig.txonly = 1;
            else the_conf.spiconfig.txonly = 0;
        }else{
            DBG("SPI needs SCK and MOSI or MISO\n");
            ret = FALSE;
            haveSPI = 0;
        }
    }
    return ret;
}

int is_disabled(uint8_t port, uint8_t pin){
    if(port > 1 || pin > 15) return TRUE;
    if(the_conf.pinconfig[port][pin].enable) return FALSE;
    return TRUE;
}

// return current conf from local `pinconfig`
int get_curpinconf(uint8_t port, uint8_t pin, pinconfig_t *c){
    CHKPINCONFIG();
    if(!c || port > 1 || pin > 15) return FALSE;
    *c = pinconfig[port][pin];
    return TRUE;
}

/**
 * @brief set_pinfunc - check if alternate function `afno` allowed on given pin
 * @param port - 0 for GPIOA and 1 for GPIOB
 * @param pin - 0..15
 * @param pcfg (io) - pin configuration
 * @return TRUE if all OK
 */
int set_pinfunc(uint8_t port, uint8_t pin, pinconfig_t *pcfg){
    DBG("set_pinfunc()\n");
    CHKPINCONFIG();
    if(is_disabled(port, pin) || !pcfg){
        DBG("Disabled?\n");
        return FALSE;
    }
    const pinprops_t *props = &pin_props[port][pin];
    switch(pcfg->mode){
    case MODE_ANALOG:
        DBG("Analog\n");
        if(!CANADC(props->funcs)){
            DBG("Can't ADC\n");
            return FALSE;
        }
        pcfg->pull = PULL_NONE; // no PullUp for analog mode
        break;
    case MODE_AF:
        DBG("Altfun\n");
        // here af is one of enum FuncValues !!! we should change `af` later
        if(pcfg->af >= FUNC_AMOUNT || !((1<<pcfg->af) & props->funcs)){
            DBG("Wrong AF\n");
            return FALSE;
        }
        pcfg->afno = props->AF[pcfg->af];
        pcfg->speed = SPEED_HIGH; // many AF needs high speed
        pcfg->otype = OUTPUT_PP; // no OD for AF
        break;
    case MODE_INPUT: // no limits
        DBG("Input\n");
        break;
    case MODE_OUTPUT: // remove pullup/pulldown for PP
        DBG("Output\n");
        if(pcfg->otype == OUTPUT_PP) pcfg->pull = PULL_NONE;
        break;
    default:
        DBG("Wrong\n");
        return FALSE;
    }
    pcfg->enable = 1; // don't forget to set enable flag!
    pinconfig[port][pin] = *pcfg;
    DBG("All OK\n");
    return TRUE;
}

/**
 * @brief get_adc_channel - get ADC channel number for given pin
 * @param port - 0/1 (GPIOA/GPIOB)
 * @param pin - 0..16
 * @return ADC channel number or -1
 */
TRUE_INLINE int8_t get_adc_channel(uint8_t port, uint8_t pin){
    if(port == 0){ // GPIOA
        if (pin <= 7) return pin; // PA0..PA7 -> IN0..IN7
    }else{ // GPIOB
        if(pin == 0) return 8; // PB0 -> IN8
        if(pin == 1) return 9; // PB1 -> IN9
    }
    return -1; // No ADC channel on this pin
}

// reinit all GPIO registers due to config; also configure (if need) USART1/2, SPI1 and I2C1
// return FALSE if found some errors in current configuration (and it was fixed to default)
int gpio_reinit(){
    bzero(monitor_mask, sizeof(monitor_mask));
    bzero(oldstates, sizeof(oldstates));
    int ret = TRUE;
    int tocopy = chkpinconf(); // if config is wrong, don't copy it to flash
    for(int port = 0; port < 2; port++){
        GPIO_TypeDef *gpio = (port == 0) ? GPIOA : GPIOB;
        for(int pin = 0; pin < 16; pin++){
            pinconfig_t *cfg = &pinconfig[port][pin];
            if(!cfg->enable) continue;
            int shift2 = pin << 1;
            gpio->MODER = (gpio->MODER & ~(3 << shift2))| (cfg->mode << shift2);
            gpio->OTYPER = (gpio->OTYPER & ~(1 << pin)) | (cfg->otype << pin);
            gpio->OSPEEDR = (gpio->OSPEEDR & ~(3 << shift2)) | (cfg->speed << shift2);
            gpio->PUPDR = (gpio->PUPDR & ~(3 << shift2)) | (cfg->pull << shift2);
            if(pin < 8){
                int shift4 = pin << 2;
                gpio->AFR[0] = (gpio->AFR[0] & ~(0xf << shift4)) | (cfg->afno << shift4);
            }else{
                int shift4 = (pin - 8) << 2;
                gpio->AFR[1] = (gpio->AFR[1] & ~(0xf << shift4)) | (cfg->afno << shift4);
            }
            if(cfg->monitor && cfg->mode != MODE_AF){
                monitor_mask[port] |= (1 << pin);
                if(cfg->mode == MODE_ANALOG){
                    if(cfg->threshold > 4095) cfg->threshold = 4095; // no threshold
                    int8_t chan = get_adc_channel(port, pin);
                    if(chan >= 0){
                        oldstates[port][pin] = getADCval(chan);
                    }
                }else{
                    // save old state for regular GPIO
                    oldstates[port][pin] = (gpio->IDR >> pin) & 1;
                }
            }
            // start/stop PWM on this pin
            if(cfg->mode == MODE_AF && cfg->af == FUNC_PWM){
                if(!startPWM(port, pin)) ret = FALSE;
            }else{ // check for collisions
                pwmtimer_t t;
                if(canPWM(port, pin, &t)){
                    if(t.collision){ // stop PWM only if "earlier" channel don't set on this
                        if((t.collport < port || t.collpin < pin) && (pinconfig[t.collport][t.collpin].af != FUNC_PWM))
                            stopPWM(port, pin);
                    }else stopPWM(port, pin);
                }
            }
        }
    }
    // if all OK, copy to the_conf
    if(tocopy) memcpy(the_conf.pinconfig, pinconfig, sizeof(pinconfig));
    else ret = FALSE;
    // TODO: configure SPI etc
    usartconf_t usc;
    if(get_curusartconf(&usc) && (usc.RXen | usc.TXen)){
        if(!usart_config(NULL)) ret = FALSE;
        else if(!usart_start()) ret = FALSE;
    }else usart_stop();
    if(haveI2C) i2c_setup((i2c_speed_t) the_conf.I2Cspeed);
    else i2c_stop();
    if(haveSPI) spi_setup();
    else spi_stop();
    return ret;
}

// get MODER for current pin
TRUE_INLINE uint32_t get_moder(volatile GPIO_TypeDef * GPIOx, uint8_t pin){
    return (GPIOx->MODER >> (pin << 1)) & 3;
}

/**
 * @brief pin_out - change pin  value
 * @param port - 0 for GPIOA, 1 for GPIOB
 * @param pin - 0..15
 * @param newval - 0 or 1 (reset/set)
 * @return FALSE if pin isn't OUT or other err
 * here I check real current settings by GPIOx->MODER
 */
int pin_out(uint8_t port, uint8_t pin, uint8_t newval){
    if(port > 1 || pin > 15) return FALSE;
    volatile GPIO_TypeDef * GPIOx = (port == 0) ? GPIOA : GPIOB;
    uint16_t mask = 1 << pin;
    uint32_t moder = get_moder(GPIOx, pin);
    if(moder != MODE_OUTPUT) return FALSE;
    if(newval) GPIOx->BSRR = mask;
    else GPIOx->BRR = mask;
    return TRUE;
}

/**
 * @brief pin_in - get current pin's value (0/1 for regular GPIO, 0..4095 for ADC)
 * @param port - 0..1
 * @param pin - 0..15
 * @return value or -1 if pin have AF or don't used
 */
int16_t pin_in(uint8_t port, uint8_t pin){
    if(port > 1 || pin > 15) return -1;
    volatile GPIO_TypeDef * GPIOx = (port == 0) ? GPIOA : GPIOB;
    uint32_t moder = get_moder(GPIOx, pin);
    int16_t val = -1;
    switch(moder){ // check REAL pin config
    case MODE_INPUT:
    case MODE_OUTPUT:
        if(GPIOx->IDR & (1<<pin)) val = 1;
        else val = 0;
        break;
    case MODE_ANALOG:{
        int8_t chan = get_adc_channel(port, pin);
        if(chan >= 0)
            val = (int16_t) getADCval(chan);
    }
        break;
    case MODE_AF:{
        pinconfig_t curconf;
        if(!get_curpinconf(port, pin, &curconf)) return -1;
        if(curconf.af == FUNC_PWM)
            val = getPWM(port, pin);
    }
        break;
    default:
        break;
    }
    return val;
}

/**
 * @brief gpio_alert - return bitmask for alerted pins (whos state changed over last check)
 *      AF don't checked! Use appropriate function for them
 * @param port - 0 for GPIOA, 1 for GPIOB
 * @return pin mask where 1 is for changed state
 */
uint16_t gpio_alert(uint8_t port){
    if(port > 1) return 0;
    if(0 == monitor_mask[port]) return 0; // nothing to monitor
    volatile GPIO_TypeDef * GPIOx = (port == 0) ? GPIOA : GPIOB;
    uint32_t moder = GPIOx->MODER;
    uint16_t curpinbit = 1; // shift each iteration
    uint16_t *oldstate = oldstates[port];
    uint16_t alert = 0;
    for(int pin = 0; pin < 16; ++pin, curpinbit <<= 1, moder >>= 2){
        uint8_t curm = moder & 3;
        if((curm == MODE_AF) || 0 == (monitor_mask[port] & curpinbit)) continue; // monitor also OUT (if OD)
        // TODO: add AIN
        if(curm == MODE_ANALOG){
            int8_t chan = get_adc_channel(port, pin);
            if(chan < 0) continue; // can't be in normal case
            uint16_t cur = getADCval(chan);
            uint16_t thresh = the_conf.pinconfig[port][pin].threshold;
            uint16_t diff = (cur > oldstate[pin]) ? (cur - oldstate[pin]) : (oldstate[pin] - cur);
            if(diff > thresh){
                oldstate[pin] = cur;
                alert |= curpinbit;
            }
        }else{
            uint16_t curval = (GPIOx->IDR & curpinbit) ? 1 : 0;
            if(oldstate[pin] != curval){
                oldstate[pin] = curval;
                alert |= curpinbit;
            }
        }
    }
    return alert;
}
