eddyem/stm32samples/F1/matrix_keyboard/main.c

/*
 * main.c
 *
 * Copyright 2015 Edward V. Emelianov <eddy@sao.ru, edward.emelianoff@gmail.com>
 *
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
 * You should have received a copy of the GNU General Public License
 * along with this program; if not, write to the Free Software
 * Foundation, Inc., 51 Franklin Street, Fifth Floor, Boston,
 * MA 02110-1301, USA.
 */

#include <stdlib.h>
#include <libopencm3/stm32/rcc.h>
#include <libopencm3/stm32/gpio.h>
#include <libopencm3/cm3/systick.h>
#include <libopencm3/usb/usbd.h>
#include <libopencm3/usb/hid.h>
#include <libopencm3/cm3/nvic.h>

#include "keycodes.h"
#include "matrixkbd.h"

const struct usb_device_descriptor dev = {
	.bLength = USB_DT_DEVICE_SIZE,
	.bDescriptorType = USB_DT_DEVICE,
	.bcdUSB = 0x0200,
	.bDeviceClass = 0,
	.bDeviceSubClass = 0,
	.bDeviceProtocol = 0,
	.bMaxPacketSize0 = 64,
// 0x03EB 0x2042  -  Atmel Keyboard Demo Application
	.idVendor = 0x03EB,
	.idProduct = 0x2042,
	.bcdDevice = 0x0200,
	.iManufacturer = 1,
	.iProduct = 2,
	.iSerialNumber = 3,
	.bNumConfigurations = 1,
};

static const uint8_t hid_report_descriptor[] = {
    0x05, 0x01, /* Usage Page (Generic Desktop)             */
    0x09, 0x06, /*		Usage (Keyboard)                    */
    0xA1, 0x01, /*		Collection (Application)            */
//    0x85, 0x02,  /*   Report ID  */
    0x05, 0x07, /*  	Usage (Key codes)                   */
    0x19, 0xE0, /*      Usage Minimum (224)                 */
    0x29, 0xE7, /*      Usage Maximum (231)                 */
    0x15, 0x00, /*      Logical Minimum (0)                 */
    0x25, 0x01, /*      Logical Maximum (1)                 */
    0x75, 0x01, /*      Report Size (1)                     */
    0x95, 0x08, /*      Report Count (8)                    */
    0x81, 0x02, /*      Input (Data, Variable, Absolute)    */
    0x95, 0x01, /*      Report Count (1)                    */
    0x75, 0x08, /*      Report Size (8)                     */
    0x81, 0x01, /*      Input (Constant)    ;5 bit padding  */
    0x95, 0x05, /*      Report Count (5)                    */
    0x75, 0x01, /*      Report Size (1)                     */
    0x05, 0x08, /*      Usage Page (Page# for LEDs)         */
    0x19, 0x01, /*      Usage Minimum (01)                  */
    0x29, 0x05, /*      Usage Maximum (05)                  */
    0x91, 0x02, /*      Output (Data, Variable, Absolute)   */
    0x95, 0x01, /*      Report Count (1)                    */
    0x75, 0x03, /*      Report Size (3)                     */
    0x91, 0x01, /*      Output (Constant)                   */
    0x95, 0x06, /*      Report Count (1)                    */
    0x75, 0x08, /*      Report Size (3)                     */
    0x15, 0x00, /*      Logical Minimum (0)                 */
    0x25, 0x65, /*      Logical Maximum (101)               */
    0x05, 0x07, /*  	Usage (Key codes)                   */
    0x19, 0x00, /*      Usage Minimum (00)                  */
    0x29, 0x65, /*      Usage Maximum (101)                 */
    0x81, 0x00, /*      Input (Data, Array)                 */
    0x09, 0x05, /*      Usage (Vendor Defined)              */
    0x15, 0x00, /*      Logical Minimum (0))                */
    0x26, 0xFF, 0x00, /* Logical Maximum (255))             */
    0x75, 0x08, /*      Report Count (2))                   */
    0x95, 0x02, /*      Report Size (8 bit))                */
    0xB1, 0x02, /*      Feature (Data, Variable, Absolute)  */
    0xC0        /* 		End Collection,End Collection       */
};
#if 0
        0x05, 0x01,          // Usage Page (Generic Desktop),
        0x09, 0x06,          // Usage (Keyboard),
        0xA1, 0x01,          // Collection (Application),
        0x75, 0x01,          //   Report Size (1),
        0x95, 0x08,          //   Report Count (8),
        0x05, 0x07,          //   Usage Page (Key Codes),
        0x19, 0xE0,          //   Usage Minimum (224),
        0x29, 0xE7,          //   Usage Maximum (231),
        0x15, 0x00,          //   Logical Minimum (0),
        0x25, 0x01,          //   Logical Maximum (1),
        0x81, 0x02,          //   Input (Data, Variable, Absolute), ;Modifier byte
        0x95, 0x01,          //   Report Count (1),
        0x75, 0x08,          //   Report Size (8),
        0x81, 0x03,          //   Input (Constant),                 ;Reserved byte
        0x95, 0x05,          //   Report Count (5),
        0x75, 0x01,          //   Report Size (1),
        0x05, 0x08,          //   Usage Page (LEDs),
        0x19, 0x01,          //   Usage Minimum (1),
        0x29, 0x05,          //   Usage Maximum (5),
        0x91, 0x02,          //   Output (Data, Variable, Absolute), ;LED report
        0x95, 0x01,          //   Report Count (1),
        0x75, 0x03,          //   Report Size (3),
        0x91, 0x03,          //   Output (Constant),                 ;LED report padding
        0x95, 0x06,          //   Report Count (6),
        0x75, 0x08,          //   Report Size (8),
        0x15, 0x00,          //   Logical Minimum (0),
        0x25, 0x68,          //   Logical Maximum(104),
        0x05, 0x07,          //   Usage Page (Key Codes),
        0x19, 0x00,          //   Usage Minimum (0),
        0x29, 0x68,          //   Usage Maximum (104),
        0x81, 0x00,          //   Input (Data, Array),
        0xc0                 // End Collection
};
#endif

static const struct {
	struct usb_hid_descriptor hid_descriptor;
	struct {
		uint8_t bReportDescriptorType;
		uint16_t wDescriptorLength;
	} __attribute__((packed)) hid_report;
} __attribute__((packed)) hid_function = {
	.hid_descriptor = {
		.bLength = sizeof(hid_function),
		.bDescriptorType = USB_DT_HID,
		.bcdHID = 0x0100,
		.bCountryCode = 0,
		.bNumDescriptors = 1,
	},
	.hid_report = {
		.bReportDescriptorType = USB_DT_REPORT,
		.wDescriptorLength = sizeof(hid_report_descriptor),
	},
};

const struct usb_endpoint_descriptor hid_endpoint = {
	.bLength = USB_DT_ENDPOINT_SIZE,
	.bDescriptorType = USB_DT_ENDPOINT,
	.bEndpointAddress = 0x81,
	.bmAttributes = USB_ENDPOINT_ATTR_INTERRUPT,
	.wMaxPacketSize = 8,
	.bInterval = 0x10,
};

const struct usb_interface_descriptor hid_iface = {
	.bLength = USB_DT_INTERFACE_SIZE,
	.bDescriptorType = USB_DT_INTERFACE,
	.bInterfaceNumber = 0,
	.bAlternateSetting = 0,
	.bNumEndpoints = 1,
	.bInterfaceClass = USB_CLASS_HID,
	.bInterfaceSubClass = 1, // boot
	.bInterfaceProtocol = 1, // keyboard
	.iInterface = 0,

	.endpoint = &hid_endpoint,

	.extra = &hid_function,
	.extralen = sizeof(hid_function),
};

const struct usb_interface ifaces[] = {{
	.num_altsetting = 1,
	.altsetting = &hid_iface,
}};

const struct usb_config_descriptor config = {
	.bLength = USB_DT_CONFIGURATION_SIZE,
	.bDescriptorType = USB_DT_CONFIGURATION,
	.wTotalLength = 0,
	.bNumInterfaces = 1,
	.bConfigurationValue = 1,
	.iConfiguration = 0,
	.bmAttributes = 0xC0,
	.bMaxPower = 0x32,

	.interface = ifaces,
};

static const char *usb_strings[] = {
	"Simple matrix keyboard 3x4",
	"EEV",
	"v01",
};

/* Buffer to be used for control requests. */
uint8_t usbd_control_buffer[128];

static int hid_control_request(usbd_device *usbd_dev, struct usb_setup_data *req, uint8_t **buf, uint16_t *len,
			void (**complete)(usbd_device *usbd_dev, struct usb_setup_data *req)){
	(void)complete;
	(void)usbd_dev;

	if ((req->bmRequestType != 0x81) ||
	   (req->bRequest != USB_REQ_GET_DESCRIPTOR) ||
	   (req->wValue != 0x2200))
		return 0;

	*buf = (uint8_t *)hid_report_descriptor;
	*len = sizeof(hid_report_descriptor);

	return 1;
}

static void hid_set_config(usbd_device *usbd_dev, uint16_t wValue){
	(void)wValue;
	(void)usbd_dev;
	usbd_ep_setup(usbd_dev, 0x81, USB_ENDPOINT_ATTR_INTERRUPT, 4, NULL);
	usbd_register_control_callback(
				usbd_dev,
				USB_REQ_TYPE_STANDARD | USB_REQ_TYPE_INTERFACE,
				USB_REQ_TYPE_TYPE | USB_REQ_TYPE_RECIPIENT,
				hid_control_request);
}

/*
 * SysTick used for system timer with period of 1ms
 */
void SysTick_init(){
	systick_set_clocksource(STK_CSR_CLKSOURCE_AHB_DIV8); // Systyck: 72/8=9MHz
	systick_set_reload(8999); // 9000 pulses: 1kHz
	systick_interrupt_enable();
	systick_counter_enable();
}

int main(void){
	usbd_device *usbd_dev;

	rcc_clock_setup_in_hsi_out_48mhz();
	SysTick_init();
/*
	// if PC11 connected to usb 1.5kOhm pull-up through transistor
	rcc_periph_clock_enable(RCC_GPIOC);
	gpio_set(GPIOC, GPIO11);
	gpio_set_mode(GPIOC, GPIO_MODE_OUTPUT_2_MHZ,
		      GPIO_CNF_OUTPUT_PUSHPULL, GPIO11);
*/
	usbd_dev = usbd_init(&stm32f103_usb_driver, &dev, &config, usb_strings, 3, usbd_control_buffer, sizeof(usbd_control_buffer));
	usbd_register_set_config_callback(usbd_dev, hid_set_config);
	matrixkbd_init();
/*
	int i;
	for (i = 0; i < 0x80000; i++)
		__asm__("nop");
	gpio_clear(GPIOC, GPIO11);
*/

	while (1){
		char prsd, rlsd;
		usbd_poll(usbd_dev);
		get_matrixkbd(&prsd, &rlsd);
		if(rlsd)
			while(8 != usbd_ep_write_packet(usbd_dev, 0x81, release_key(), 8));
		if(prsd)
			while(8 != usbd_ep_write_packet(usbd_dev, 0x81, press_key(prsd), 8));
	}
}

volatile uint32_t Timer = 0; // global timer (milliseconds)
/**
 * SysTick interrupt: increment global time & send data buffer through USB
 */
void sys_tick_handler(){
	Timer++;
}
