eddyem/stm32samples/F3:F303/MLX90640-allsky/main.c

/*
 * This file is part of the ir-allsky project.
 * Copyright 2025 Edward V. Emelianov <edward.emelianoff@gmail.com>.
 *
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
 * You should have received a copy of the GNU General Public License
 * along with this program.  If not, see <http://www.gnu.org/licenses/>.
 */

#include "adc.h"
#include "hardware.h"
#include "heater.h"
#include "i2c.h"
#include "mlxproc.h"
#include "commproto.h"
#include "strfunc.h"
#include "usart.h"
#include "usb_dev.h"

#define MAXSTRLEN    RBINSZ

volatile uint32_t Tms = 0;

void sys_tick_handler(void){
    ++Tms;
}

static const char *const scanend = "SCANEND\n", *const foundid = "FOUNDID=";

int main(void){
    char inbuff[MAXSTRLEN+1];
    if(StartHSE()){
        SysTick_Config((uint32_t)72000); // 1ms
    }else{
        StartHSI();
        SysTick_Config((uint32_t)48000); // 1ms
    }
    USBPU_OFF(); // for development board with managed pullup resistor
    hw_setup();
    adc_setup();
    i2c_setup(I2C_SPEED_400K);
    bme_init();
    usart_setup(115200);
    // setup USB DP as alternate function - for sensors' board with constant pullup resistor
    GPIOA->MODER = (GPIOA->MODER & ~GPIO_MODER_MODER12) | MODER_AF(12);
    USBPU_ON();
    USB_setup();
    // set senders for abiliby of sending messages between interfaces
    set_senders(USB_sendstr, USB_putbyte, USB_send, usart_sendstr, usart_putbyte, usart_send);
    uint32_t ctr = Tms, Tlastima[N_SENSORS] = {0};
    mlx_continue(); // init state machine
    while(1){
        IWDG->KR = IWDG_REFRESH;
        if(Tms - ctr > 499){
            ctr = Tms;
            if(!mlx_nactive()){ mlx_stop(); mlx_continue(); }
            pin_toggle(GPIOB, 1 << 1 | 1 << 0); // toggle LED @ PB0
        }
        int l = USB_receivestr(inbuff, MAXSTRLEN);
        if(l < 0) USB_sendstr("USBOVERFLOW\n");
        else if(l){
            const char *ans = parse_cmd(USB_sendstr, inbuff);
            if(ans) USB_sendstr(ans);
        }
        if(i2c_scanmode){ // send this to both
            uint8_t addr;
            int ok = i2c_scan_next_addr(&addr);
            if(addr == I2C_ADDREND){
                USB_sendstr(scanend); USB_putbyte('\n');
                usart_sendstr(scanend); usart_putbyte('\n');
            }else if(ok){
                const char *straddr = uhex2str(addr);
                USB_sendstr(foundid); USB_sendstr(straddr); USB_putbyte('\n');
                usart_sendstr(foundid); usart_sendstr(straddr); usart_putbyte('\n');
            }
        }
        IWDG->KR = IWDG_REFRESH;
        mlx_process();
        if(cartoon && CDCready) for(int i = 0; i < N_SENSORS; ++i){ // USB-only
            uint32_t Tnow = mlx_lastimT(i);
            if(Tnow != Tlastima[i]){
                fp_t *im = mlx_getimage(i);
                if(im){
                    sendfun_t cursender = get_sender();
                    set_sender(USB_sendstr);
                    U(Timage); USB_putbyte('0'+i); USB_putbyte('='); UN(u2str(Tnow));
                    drawIma(im);
                    Tlastima[i] = Tnow;
                    set_sender(cursender);
                }
            }
        }
        usart_process();
        if(usart_ovr()) usart_sendstr("USART_OVERFLOW\n");
        char *got = usart_getline(NULL);
        if(got){
            const char *ans = parse_cmd(usart_sendstr, got);
            if(ans) usart_sendstr(ans);
        }
        bme_process();
        heater_process();
    }
}
