eddyem/stm32samples/F0:F030,F042,F072/usbcan_gpio/gpio.h

/*
 * This file is part of the usbcangpio project.
 * Copyright 2026 Edward V. Emelianov <edward.emelianoff@gmail.com>.
 *
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
 * You should have received a copy of the GNU General Public License
 * along with this program.  If not, see <http://www.gnu.org/licenses/>.
 */

#pragma once

#include <stdint.h>
#include <stm32f0.h>

#ifdef EBUG
#define USBIF   IGPIO
#include "strfunc.h"
#define DBG(x)  SEND(x)
#define DBGNL() NL()
#else
#define DBG(x)
#define DBGNL()
#endif


// MODER
typedef enum{
    MODE_INPUT = 0,
    MODE_OUTPUT = 1,
    MODE_AF = 2,
    MODE_ANALOG = 3
} pinmode_t;

// PUPDR
typedef enum{
    PULL_NONE = 0,
    PULL_UP = 1,
    PULL_DOWN = 2
} pinpull_t;

// OTYPER
typedef enum{
    OUTPUT_PP = 0,
    OUTPUT_OD = 1
} pinout_t;

// OSPEEDR
typedef enum{
    SPEED_LOW = 0,
    SPEED_MEDIUM = 1,
    SPEED_HIGH = 3
} pinspeed_t;

// !!! FuncNames means position of bit in funcvalues_t.flags!
typedef enum FuncNames{ // shift 1 by this to get "canUSART" etc; not more than 7!
    FUNC_AIN = 0,
    FUNC_USART = 1,
    FUNC_SPI = 2,
    FUNC_I2C = 3,
    FUNC_PWM = 4,
    FUNC_AMOUNT // just for arrays' sizes
} funcnames_t;

/*
typedef union{
    struct{
        uint8_t canADC : 1;
        uint8_t canUSART : 1;
        uint8_t canSPI : 1;
    };
    uint8_t flags;
} funcvalues_t;
*/
typedef struct{
    uint8_t enable : 1;  // [immutable!] pin config avialable (==1 for PA0-PA3, PA5-PA7, PA9, PA10, PB0-PB7, PB10, PB11, ==0 for rest)
    pinmode_t mode : 2;
    pinpull_t pull : 2;
    pinout_t otype : 1;
    pinspeed_t speed : 2;
    uint8_t afno : 3;    // alternate function number (only if mode == MODE_AF)
    funcnames_t af : 3;  // alternate function name (`FuncNames`)
    uint8_t monitor : 1; // monitor changes
    uint16_t threshold;  // threshold for ADC measurement
} pinconfig_t;

typedef struct{
    uint8_t isrx : 1;
    uint8_t istx : 1;
} usart_props_t;

typedef struct{
    uint8_t isscl : 1;
    uint8_t issda : 1;
} i2c_props_t;

typedef struct{
    uint8_t issck  : 1;
    uint8_t ismiso : 1;
    uint8_t ismosi : 1;
} spi_props_t;

/*
typedef struct{
    uint32_t speed;
    uint8_t cpol : 1;
    uint8_t cpha : 1;
    uint8_t lsbfirst : 1;
    uint8_t enabled : 1;
} spiconfig_t;
*/

int is_disabled(uint8_t port, uint8_t pin);
int pinfuncs(uint8_t port, uint8_t pin);
int chkpinconf();

int set_pinfunc(uint8_t port, uint8_t pin, pinconfig_t *pcfg);
int get_curpinconf(uint8_t port, uint8_t pin, pinconfig_t *c);

int get_usart_index(uint8_t port, uint8_t pin, usart_props_t *p);
int get_i2c_index(uint8_t port, uint8_t pin, i2c_props_t *p);
int get_spi_index(uint8_t port, uint8_t pin, spi_props_t *p);

int gpio_reinit();

int pin_out(uint8_t port, uint8_t pin, uint8_t newval);
int16_t pin_in(uint8_t port, uint8_t pin);
uint16_t gpio_alert(uint8_t port);
